jakubprzybytek/AstroWeather/sst/docs/api.md

# Main Forecast API

## Story

As an AstroWeather client, I want to request the forecast for a configured
location so that I can display its weather and astronomical events together for
the next six observing nights.

The endpoint presents one location-centric view. Clients should not need to
know which data is calculated on demand, which data is stored, or which weather
supplier produced it.

## Scope

For a valid `configurationId`, the main endpoint returns:

- the configuration identifier;
- the local date and time at which the response was rendered, which the
  device uses to synchronize its real-time clock;
- six observing nights, starting with the current night in the configuration's
  local timezone;
- local sunset and next-day sunrise times for each night;
- fixed-size hourly sun, moon, cloud, and precipitation matrices for each
  night, graded in four levels, with thunderstorms blinking;
- the supported display board identifier for each night;
- available maximum and minimum temperature for each night;

An observing night is the local-noon-to-local-noon window already used by
weather ingestion. Its `nightId` is the local calendar date on which the window
starts. For example, `nightId = 2026-09-17` covers local noon on September 17
through local noon on September 18.

## Endpoint

```http
GET /astro/{configurationId}
```

This is the main forecast endpoint, for signed-in web users. The device
calls the same handler as

```http
GET /device/astro/{configurationId}?key=<device key>
```

Both are served over HTTPS only. See
[Access control](architecture.md#access-control) for the credentials each
needs; without one the API answers `401` (no credential) or `403` (wrong
device key) instead of the payload.

### Demo configuration `test`

`GET /astro/test` (and `GET /device/astro/test` with the device key) returns a
made-up forecast that shows every display variant, for trying the boards out.
`test` is not in `configurations.ts` and is not listed by
`GET /configurations`; the web UI offers it on the Home view only, and the
device fetches it with `astro test` (or with `api path /device/astro/test`).
The payload is a normal protocol 3 response for six consecutive nights
(`forecast/demo.ts`):

- `time` is the real time in Europe/Warsaw, since the device sets its clock
  from it; `lastWeatherFetchTime` and the four aurora fetch times are `?`, and
  `refreshIntervalMinutes` is `360`.
- Sunset and sunrise start at random times and move by 1–3 minutes a night;
  the moon rises 40–60 minutes later each night. The sun and moon rows follow
  those times.
- Each night has a theme: clear sky with an aurora storm blinking "now";
  overcast with rain; thunderstorms clearing; a frosty evening clouding over
  with an aurora burst; every level and blink in turn; and missing data (gaps,
  whole-row `?`, unavailable temperatures and moon). Together the cloud,
  precipitation and aurora rows use every cell character.
- Temperatures cover one and two digits, both signs and zero (`4`, `-3`,
  `17`, `28`, `-14`, `0`), and `?`.

## Response Format

The endpoint is consumed by an STM32-based device without a JSON parser. A
successful request returns `text/plain; charset=utf-8` using the versioned ASCII
`key=value` protocol defined in [api-payload.md](api-payload.md).

The response contains the `protocol=3`, `configurationId`, `time`,
`lastWeatherFetchTime`, `lastGfzFetchTime`, `lastNoaaKpFetchTime`,
`lastNoaaOutlookFetchTime`, `lastOvationFetchTime` and `refreshIntervalMinutes`
header records, followed by six fixed-order display blocks. `time` is the configuration's local wall-clock time with its UTC
offset as `YYYY-MM-DDTHH:MM:SS.mmm+HH:MM`; `lastWeatherFetchTime` is the local
`YYYY-MM-DDTHH:MM:SS+HH:MM` of the last successful weather fetch, or `?`, and
the four aurora records are the same for each aurora feed. Each block contains, in order,
`display`, `board`, `nightId`, `numeric_0`, `numeric_1`, `matrix_0` through
`matrix_4`, `numeric_2`, and `numeric_3`. `numeric_0` and `numeric_1`
are sunset and sunrise; `matrix_0` through `matrix_4` are sun, moon, cloud,
precipitation and aurora; and `numeric_2` and `numeric_3` are maximum and minimum
temperature. `board` is `num4x4_matrix5x21` in version 3.
`refreshIntervalMinutes` is `60` on a storm night and `360` otherwise.

Records remain present when a source is missing or fails and use the payload
sentinel `?` for all unavailable times, weather values, and matrix slots. There is no
`displayCount` or end marker in version 3. The wire
format has one empty row between display blocks and no comments.

Error responses use the same line protocol and stable machine-readable error
identifiers. HTTP status codes remain authoritative.

## Behavior

### Forecast window

The handler determines the current `nightId` using the configuration's timezone
and the local-noon boundary. It returns that night plus the following five
nights in ascending `nightId` order.

The six-night window is stable around UTC midnight because it is derived from
the location's local time. Tests should inject the current time so the boundary
before and after local noon is deterministic.

### Response time

The `time` header record is the configuration's local wall-clock time, read
from the server clock after the forecast has been assembled so it is as close
as possible to the moment the response is sent. It uses the same IANA timezone
and DST rules as the forecast window, carries milliseconds, and ends in the UTC
offset in force at that instant (`+02:00`, `+01:00`), so a reader can tell
which zone it is in. The embedded device sets its real-time clock from the
wall-clock part.

### Last weather fetch time

`lastWeatherFetchTime` is the newest `fetchedAt` among the weather items used in
the response, converted to the configuration's local time, truncated to the
second, and followed by the UTC offset in force at the fetch. An ingestion run writes a night's item only after fetching and parsing
it, so a failed run leaves the value at the last success, and the value grows
old when ingestion keeps failing. It is `?` when no weather item is available.
The record is specific to weather: a future source adds its own record rather
than sharing this one.

### Last aurora fetch times

Each aurora feed has its own record, built the same way from the `fetchedAt`
of that feed's `#AURORA` items for the six nights served:

| Record | Feed | Item |
|---|---|---|
| `lastGfzFetchTime` | GFZ Hp60 forecast, nights 1–3 | `#AURORA#GFZ` |
| `lastNoaaKpFetchTime` | NOAA 3-day Kp forecast, nights 1–3 | `#AURORA#NOAA3` |
| `lastNoaaOutlookFetchTime` | NOAA 27-day outlook, nights 4–7 | `#AURORA#NOAA27` |
| `lastOvationFetchTime` | NOAA OVATION nowcast | `#AURORA#OVATION` |

The forecast job writes a feed's item only when that feed was fetched and
parsed, so one failing feed shows as an old time while the others stay
current; a single aurora record would hide that. The nowcast rewrites the
`OVATION` item each time it samples, which happens only on a storm night after
dark, so `lastOvationFetchTime` is normally `?`. A record is `?` when none of
the feed's items is there, and all four are `?` when the aurora read fails.
The `FLAG` item is not a feed and has no record. The demo configuration sends
`?` for all four.

### Astronomy

Astronomical events are calculated for each night from the configured latitude
and longitude. Sunset belongs to the date that starts the night, and sunrise
belongs to the following local date. Moonrise and moonset times are not
emitted; the moon is represented only by its hourly above-horizon matrix.

Sunset and sunrise are serialized as local `HH:MM` values. An event that does
not occur is represented by `?`. Sun and moon are graded for the 21
local-hour slots, 14:00 through 10:00 on the following date, by the minutes
of each hour the body is above the horizon: `0` for none, `1` for under half
an hour, `2` for half an hour or more, `3` for the whole hour. The altitude
is sampled at the middle of every minute. The 11:00-12:00 interval is not
displayed. The server emits the same 21 wall-clock slots across DST
transitions and maps each local hour to the appropriate instant.

`matrix_2` grades total cloud coverage: `0` only for a clear sky (0 %), and
the rest in thirds, `1` for 1-33 %, `2` for 34-66 % and `3` for 67-100 %.
`matrix_3` grades the precipitation probability in quarters (`0` for 0-24 % up
to `3` for 75-100 %), with `*` for a slot where a thunderstorm is predicted.
An available matrix contains exactly 21 characters, each `0`-`3`, `*` or `?`;
a matrix row with no available source data is represented by the single `?`
character.
Within an available row, `?` represents an unavailable individual slot. The
device shows `*` as its brightest level blinking; see
[api-payload.md](api-payload.md#matrix-encoding).

### Weather

Weather is read from the `ForecastData` DynamoDB table using the location
partition and requested night range:

```text
PK = LOC#<configurationId>
SK = NIGHT#<nightId>#WEATHER
```

Only `#WEATHER` records are part of the main API.

DynamoDB TTL removal is asynchronous. The reader must exclude an item when
`expireAt` is at or before the request time, even if DynamoDB has not deleted it
yet. Temperature extrema are calculated only from hourly values within the
requested observing night. The maximum is serialized in `numeric_2` and the
minimum in `numeric_3`, each rounded to whole degrees and written without a
decimal point (Clear Outside reports whole degrees).

### Graceful degradation

Astronomy and weather are assembled independently. Missing, expired, or failed
weather retrieval must not prevent available astronomy from being returned.
The affected weather matrix slots and weather-derived numeric values use `?`.

Likewise, an astronomy calculation failure must not prevent available weather
from being returned. The affected sunset and sunrise values and sun or moon
matrix slots use `?`.

The endpoint always returns all six display blocks with the complete fixed
record shape. It returns `500` only when it cannot assemble a trustworthy
protocol response at all; a failure isolated to astronomy or weather returns
`200` with sentinels only for the unavailable fields. Failures are logged with
their source and affected nights.

### Rate limiting and caching

API Gateway limits the API to a burst of one request and a steady-state rate of
one request per second. Requests beyond these limits are throttled by API
Gateway. The API does not currently emit cache headers or use response caching.

## Errors

| Status | Body | When |
|---|---|---|
| `200` | Forecast response | The configuration exists, including when astronomy or weather is partly unavailable |
| `404` | `error=configuration_not_found` response | The identifier is missing or unknown |
| `401` | `{"message":"Unauthorized"}` from API Gateway | No Cognito token on `/astro/...`, or no `key` on `/device/astro/...` |
| `403` | `{"message":"Forbidden"}` from API Gateway | Wrong device key |
| `429` | API Gateway's throttling response | Over the stage's one request per second |
| `500` | `error=forecast_unavailable` response | No trustworthy protocol response can be assembled |

The API does not expose upstream errors, AWS details, or stack traces to the
client. Operational details belong in structured Lambda logs.

## Acceptance Criteria

1. A request for a known configuration returns `200`, content type `text/plain`,
   protocol version 3, and exactly six display blocks in ascending order.
2. The first night is selected using the location's timezone and local-noon
   boundary; the next five night identifiers are consecutive local dates.
3. Every display block contains the complete, fixed-order record set defined in
   `api-payload.md`; each matrix is either `?` or exactly 21 valid characters.
4. Available, unexpired `#WEATHER` records supply the matching nights' minimum
   and maximum temperatures.
5. Expired, out-of-range, and other service records are not returned as weather.
6. Missing or failed weather does not remove a display block or available
   astronomy; its numeric values and unavailable matrix rows or slots use
   `?`.
7. An unknown configuration returns the versioned text error payload with
   status `404`.
8. Failed astronomy does not remove a display block or available weather; its
   times and unavailable sun or moon matrix rows or slots use `?`.
9. Unit tests cover the local-noon boundary, six-night range, item grouping,
   expired-item filtering, independent astronomy and weather failures, matrix
   encoding, sentinels, and serialization order.
10. An integration test verifies the deployed route for one known and one
   unknown configuration.
11. A successful response carries `time` as the configuration's local
   `YYYY-MM-DDTHH:MM:SS.mmm+HH:MM` at render time, with the offset of that
   instant, including after a DST change.
12. A successful response carries `lastWeatherFetchTime` as the local time and
   UTC offset of the newest weather `fetchedAt` used, or `?` without weather,
   and one such record per aurora feed, `?` for a feed without items.
13. Available `#AURORA` items supply `matrix_4`, merged as in
   [aurora-forecast-supplier.md](aurora-forecast-supplier.md#merging-sources);
   missing or failed aurora leaves it `?` and `refreshIntervalMinutes=360`
   without affecting the other rows.

## Data Attribution

The aurora row uses:

- the GFZ Hp60 and Kp forecasts, GFZ German Research Centre for Geosciences,
  licensed CC BY 4.0: Matzka, J., Bronkalla, O., Tornow, K., Elger, K. and
  Stolle, C. (2021), Geomagnetic Kp index, GFZ Data Services,
  doi:10.5880/Kp.0001; Matzka, J., Stolle, C., Yamazaki, Y., Bronkalla, O. and
  Morschhauser, A. (2021), The geomagnetic Kp index and derived indices of
  geomagnetic activity, Space Weather, doi:10.1029/2020SW002641;
- the 3-day Kp forecast, the 27-day outlook and the OVATION aurora nowcast of
  the NOAA Space Weather Prediction Center (public domain).

## Non-goals

- Backfilling or migrating old DynamoDB records.
- Fetching Clear Outside during an API request.
- Configuration CRUD or accepting arbitrary coordinates.
- Additional forecast services beyond weather and aurora.
- Guaranteeing that weather exists for every requested night.

## Clients

- **Embedded device**: calls `/device/astro/{configurationId}` with its key
  and parses the line protocol as described in
  [api-payload.md](api-payload.md).
- **Web UI**: a protocol inspection tool. It shows the HTTP status, content
  type, and response body verbatim, and deliberately does not parse the line
  protocol.
