jakubprzybytek/AstroWeather/firmware/HostControllerA/Docs/Console.md

# USB Console and Log

## Overview

The board enumerates as a USB CDC virtual COM port. That one port carries two
things:

- **The log.** Every task writes diagnostics through `LogService`, which is the
  only code that transmits on the port.
- **The console.** `ConsoleService` reads lines typed on the host, runs them as
  commands, and replies through the same log.

Both are HostController features. The DisplayController project has no USB and
no console yet; see [DisplayController](#displaycontroller).

The port, the client tools and recovering a port that has vanished are in
[Development.md](../../Docs/Development.md#connecting-over-usb-cdc).

## USB Device

The STM32G0B1's full-speed USB peripheral (`PA11`/`PA12`) runs ST's CDC class
from `USB_Device/`, generated by CubeMX. It enumerates as `VID_0483&PID_5740`
with a serial number built from the chip's unique ID (`Get_SerialNum()` in
`USB_Device/App/usbd_desc.c`), so Windows keeps giving it the same COM number.
`defaultTask` calls `MX_USB_Device_Init()` once the scheduler runs and then
exits; from then on USB runs from its interrupt.

| Item | Setting |
| --- | --- |
| Clock | HSI48, kept within USB's 0.25 % by the clock recovery system (CRS), synchronised to the host's start-of-frame packets. `main()` starts the CRS from `TRIM` 64; see [Development.md](../../Docs/Development.md#settings-that-must-survive-regeneration). |
| Interrupt | `USB_UCPD1_2_IRQn` at priority 1, above every other interrupt (all at 3); see [Architecture.md](Architecture.md#interrupt-priorities). |
| Receive | `CDC_Receive_FS()`, in the interrupt, hands each packet to `ConsoleService_OnUsbRxData()` and rearms reception. |
| Transmit | Only `LogService` calls `CDC_Transmit_FS()`; see [Log Service](#log-service). |
| Link power management | Off in the hardware configuration; no BOS descriptor, which suits a USB 2.00 device. |

**Why priority 1.** While an EP0 receive (`CTR_RX`) is still pending, the
peripheral does not answer a new SETUP packet, and the PC fails a request
after three quick tries. The display refresh interrupt holds the CPU for up to
about 170 us a thousand times a second, and a USB interrupt itself takes 100 to
290 us in the Debug build, so at the same priority Windows' requests were
sometimes missed: error 31 when opening the port, or a failed enumeration with
a new COM number. Above the refresh, USB is serviced at once.

The cost is on the display: a USB interrupt can now nest inside the refresh
interrupt, so the refresh's longest interrupt time in `status` can read several
hundred microseconds and a burst of USB requests can add a few late shifts.
Ordinary console use adds none. How the cause was found is in the
[archive](archive/USB_COM_Port_Investigation.md).

## Welcome Message

Opening the port prints a welcome, so a connected device is visibly alive even
with statistics off:

```text
[0:00:05:12] [INFO] OK connected to AstroWeather HostController, build 42, built 2026-09-23 10:12:40
[0:00:05:12] [INFO] Settings loaded from EEPROM: ok
[0:00:05:12] [INFO] 5 warnings/errors kept ('errors' lists them); newest: W 2026-09-27 12:19:50: DisplayBoard 0x14 unreachable status=1
[0:00:05:12] [INFO] Type 'help' for commands. Periodic stats are off; 'stats on' to switch.
```

The third line appears only while the [error log](#error-log) holds entries.

The build number and time come from `../Common/cmake/BuildInfo.cmake`, which
counts every build in `BUILD_NUMBER` and regenerates both, so they identify
the flashed image ([Development.md](../../Docs/Development.md#build)). The settings line gives
`Settings::Store::describe()` of the boot-time load (`ok`, `blank`,
`bad-crc`, ...; see [Settings.md](Settings.md#decode-results)). It is repeated
here because the startup log is written before USB has enumerated and never
reaches the host.

The welcome is triggered from two CDC class requests, hooked in the `USER CODE`
section of `USB_Device/App/usbd_cdc_if.c`:

| Request | Bridge call | Why |
| --- | --- | --- |
| `SET_CONTROL_LINE_STATE` | `ConsoleService_OnHostLineState(dtr)` | A rising edge of DTR. pyserial and `astro_console.py` raise DTR on open. |
| `SET_LINE_CODING` | `ConsoleService_OnHostLineCoding()` | Every terminal sets the line coding on open, including ones that never raise DTR, such as HTerm by default. |

Both only set a thread flag; the welcome is sent from the console task. A
program that sends both does so within milliseconds, so the task prints at most
one welcome per second (`kWelcomeHoldoffMs`). Changing the baud rate in a
terminal that is already open sends `SET_LINE_CODING` again and repeats the
welcome.

## Output Format

Every line on the port, a command reply or a log message, is a log record:

```text
[d:hh:mm:ss] [LEVEL] text
```

The prefix is uptime from `HAL_GetTick()`, with days unpadded. Command replies
are logged at `INFO`, so a reply looks like
`[0:00:05:20] [INFO] OK time-display=on`. The examples below leave the prefix
out.

| Level | Tag | ANSI colour |
| --- | --- | --- |
| `Info` | `INFO` | none |
| `Warn` | `WARN` | yellow, `ESC[33m` |
| `Error` | `ERR` | red, `ESC[31m` |
| `Debug` | `DEBUG` | dark grey, `ESC[90m` |

A coloured line is sent as `ESC[..m` + text + `ESC[0m` + `\n`.

Log messages from other tasks arrive interleaved with command replies. Replies
to a single command are queued together by the console task and are not split
by other output in practice, but asynchronous results, such as those of
`astro refresh`, follow later among ordinary log lines.

### ST67 driver messages

The ST67W6X network driver logs through `vLoggingPrintf()`, which
`User/Src/WiFi/St67HttpFetchTask.cpp` redirects into `LogService`. The driver's
`LOG_LEVEL` is `LOG_DEBUG` (`ST67W6X_Network_Driver/Target/logging_config.h`),
so its info and debug messages both appear, at the `DEBUG` level. Errors map to
`ERR` and warnings to `WARN`. The driver's file and line are dropped and each
message is truncated to 95 characters. Driver messages usually end in their own
`\n`, so they are followed by a blank line. Raw AT command logging
(`W61_AT_LOG_ENABLE`) is off.

## Log Service

`LogService` (`User/Src/Debug/LogService.cpp`) is a `Task<1536>` at normal
priority, started first in the HostController's `AstroWeather_Init()`.

Producers call `log()`, `logf()` or `sendLine()` from task context. The call
formats the prefix and message into a 256-byte record, puts it on a static
16-entry CMSIS queue without blocking, and wakes the task. If the queue is full,
the oldest record is discarded to make room; each lost record counts as
`dropped`. The calls are not ISR-safe.

The task drains the queue and hands each record to `CDC_Transmit_FS()`, the only
caller of that function in the application. While the transport reports
`USBD_BUSY` it retries every 5 ms, for up to 40 ms, then drops the record and
counts `busyDrop`. Any other failure also counts `busyDrop`. `CDC_Transmit_FS()`
reports busy before USB has enumerated, and the previous packet stays pending
while no program has the port open, so output written with the port closed is
lost rather than buffered. A queued record is removed before it is sent, so an
accepted record can still be lost here.

### Burst size

The console and log tasks have the same priority, so a command's whole reply is
normally queued before any of it is sent. A reply of more than 16 lines would
push its own first lines out. `help` and `errors` send through
`Console::PacedOutput` (`User/Src/Console/PacedOutput.cpp`), which pauses
30 ms after every 8 lines so the log task can drain the queue; `help all`,
over 200 lines, arrives whole. `status` is kept under 16 lines by a comment in
`StatusCommand.cpp`. `eeprom dump` prints 32 lines and relies on the log task
getting time between the I2C reads; a `dropped` count that rises during a dump
means lines were lost.

### Statistics

`stats on` switches on periodic telemetry: once immediately, then every 5
seconds on a fixed schedule, whatever else is being logged. It is off at every
boot and not saved. All of it is sent at the `Debug` colour and bypasses the
queue.

```text
[0:00:06:40] [STATS] sent=412 dropped=0 busyDrop=37
[0:00:06:40] [MEM] heapFree=24752 heapMin=19352
[0:00:06:40] [STACK] name=LogService configured=1536 remaining=652
[0:00:06:40] [STACK] name=ConsoleService configured=2816 remaining=1692
...
```

| Field | Meaning |
| --- | --- |
| `sent` | Queued records transmitted, command replies included. Statistics lines are not counted. |
| `dropped` | Records lost because the queue was full. |
| `busyDrop` | Lines lost because USB stayed busy or no host had the port open. Statistics lines are counted here. |
| `heapFree`, `heapMin` | `xPortGetFreeHeapSize()` and `xPortGetMinimumEverFreeHeapSize()`, in bytes. |
| `configured` | The task's stack size in bytes. |
| `remaining` | Stack high-water mark in bytes: the part of the stack never yet used. |

There is one `[STACK]` line for each task created through `Task<>`. The counters
are cumulative since boot. See [Firmware-RAM-Usage.md](Firmware-RAM-Usage.md)
for what the stack figures mean for sizing.

## Error Log

`LogService` keeps every message logged at `Warn` or `Error` in
`ErrorLog` (`User/Src/Debug/ErrorLog.cpp`), on top of printing it. That
includes the ST67 WiFi driver's own errors, which arrive through
`vLoggingPrintf()`. It is read with [`errors`](#errors) and summed up in the
[welcome message](#welcome-message), so a problem that happened while no
terminal was open, or before USB enumerated at boot, is still visible.

- **24 entries, ordered by latest occurrence.** The list runs from the entry
  quiet longest to the latest problem, which is also the "newest" the welcome
  message shows. When all 24 are used, the entry quiet longest is overwritten
  and counted as dropped, so a problem that keeps recurring is not pushed out
  by one-off ones.
- **Repeats are one entry.** A message identical to one already kept, at the
  same level, bumps that entry's count and last time and moves it to the end;
  its first time stays. So an error repeated every retry, or the five
  `DisplayBoard 0x1x unreachable` warnings of every refresh, take one entry
  each. Each entry stores a 16-bit hash of its text, so a new message is
  compared in full only against entries with the same hash.
- **Across resets.** An entry dated throughout and a dated repeat merge even
  across a reset, since a date means the same before and after it. Uptime
  restarts at every boot, so an entry with an uptime stamp, or a repeat
  logged before the clock is set, only merges within its own boot; each entry
  records the boot of its latest occurrence for that. The log therefore does
  not show that a merged problem spanned a reset.
- **Order without copying.** The 180-byte entries stay in their slots; a
  24-byte `order` list gives the slots by latest occurrence, so moving an
  entry to the end shifts at most 23 bytes with interrupts masked, not up to
  4.3 KB of entries.
- **Timestamps.** The local date and time when the clock is set, read from
  the RTC registers directly (`ClockTask::wallSecondsNow()`), without the RTC
  mutex, so a task that logs while holding it cannot deadlock. Until the clock
  is set, which after a power-up is the first astro refresh, entries carry
  uptime instead, marked `(previous boot)` or `(<n> boots ago)` when listed
  after a reset.
- **Text.** Up to 159 characters of the message; longer ones are cut. That
  keeps every warning and error whole except the longest ST67 statistics,
  such as `ST67 batch-final ...`.
- **Kept over a reset, a crash and reflashing, not a power loss.** The log
  lives in a 5 KB RAM region that the startup code neither initialises nor
  clears (`.noinit`, the last 5 KB of RAM, set up in `STM32G0B1xx_FLASH.ld`),
  at the same address in every build. At boot, `ErrorLog::Log::begin()` keeps
  it if its magic word and check word match and every entry is consistent,
  otherwise starts empty, and counts the boot. After a power loss the region
  is random and fails the check. A change to the entry layout must bump
  `ErrorLog::kVersion`, so an older layout is discarded rather than misread.
- **Cost.** Recording masks interrupts for the copy of one entry, under 200 bytes
  (the hash is computed before), so it is safe from any task or interrupt.
  Messages logged before `LogService::init()` are not recorded.

Only the HostController has the log.

## Console Service

`ConsoleService` (`User/Src/Console/ConsoleService.cpp`) is a `Task<2816>` at
normal priority.

### Receive path

1. `CDC_Receive_FS()` in `usbd_cdc_if.c` runs in the USB interrupt and passes
   each packet to `ConsoleService_OnUsbRxData()`, declared in
   `User/Inc/Console/ConsoleServiceBridge.h`, then rearms reception.
2. The bytes go into a 256-byte single-producer, single-consumer ring, and the
   task is woken. Bytes that arrive while the ring is full are discarded
   silently.
3. The task assembles lines from the ring:
   - `\r` is ignored and `\n` ends the line.
   - A line holds at most 127 characters. Anything longer is discarded up to
     the `\n` and answered with `ERR line-too-long`.
   - An empty line is ignored.
4. A complete line goes onto an 8-deep command queue. If it is full, the line is
   dropped with `ERR command-queue-full`.
5. The task runs queued commands one at a time, on its own stack.

Input is not echoed. The only output for a command is its reply.

### Dispatch

Each handler is tried in turn; the first that recognises the line owns it:

1. `help` (`HelpCommand.cpp`)
2. `errors [clear]` (`ErrorsCommand.cpp`), HostController only
3. `status` (`StatusCommand.cpp`)
4. `stats on`, `stats off` (in `ConsoleService.cpp`)
5. `astro ...` (`AstroCommand.cpp`), HostController only
6. `time ...` (`TimeCommand.cpp`), HostController only
7. `api ...` (`ApiCommand.cpp`), HostController only
8. `display low [on|off]` (`LowBrightnessCommand.cpp`), HostController only;
   ahead of `display`, which would take it as a bad argument
9. `adc ...` (`AdcCommand.cpp`)
10. `settings ...` and `wifi ...` (`SettingsCommand.cpp`)
11. `eeprom ...` (`EepromCommand.cpp`)
12. `display ...` (`DisplayCommand.cpp`)

A line no handler recognises gets `ERR invalid-command`. Commands are
case-sensitive. Fixed commands such as `stats on` or `settings show` must match
exactly, with single spaces; commands with numeric arguments are parsed with
`sscanf` and are more forgiving about spacing.

Handlers return a `Console::CommandResult`, and `ConsoleService` turns the
failures into these replies:

| Reply | Meaning |
| --- | --- |
| `ERR invalid-command` | No handler recognised the line. |
| `ERR invalid-argument` | The command was recognised but its arguments were not. |
| `ERR rtc-unavailable` | The RTC could not be read or written. |
| `ERR settings-unavailable` | No settings store, or the EEPROM write failed. A failed write is also logged as `[ERR] Settings save failed status=<n>`. |
| `ERR eeprom-unavailable` | No EEPROM in this variant, or the chip did not answer. |
| `ERR display-unavailable` | No display in this variant. |
| `ERR display-unreachable 0x1x`, `ERR unsupported-remote` | See [display](#display). |
| `ERR astro-refresh-busy`, `ERR astro-refresh-unavailable` | See [astro](#astro). |

Some handlers, `help`, `settings` and `wifi` among them, send their own more
specific `ERR` lines instead.

## Command Reference

Commands marked **HC** exist only in the HostController build. `help` lists
the same commands on the device.

### help

| Command | Reply |
| --- | --- |
| `help` | `OK help`, then every command's usage and one-line summary, by group. |
| `help <group>` | `OK help <group>`, then the group's commands, each with its summary, details and examples, then the group's notes. |
| `help <group> <command>` | `OK help <group> <command>`, then that command alone, e.g. `help display show` or `help time display`. The words must start the command's usage. |
| `help all` | `OK help all`, then every group in full, about 220 lines. |
| `help <unknown>` | `ERR unknown help group '<name>'; groups: status, stats, errors, display, astro, api, time, adc, settings, wifi, eeprom` |
| `help <group> <unknown>` | `ERR no help for '<group> <words>'; 'help <group>' lists its commands` |

The groups are `status`, `stats`, `errors` (HC), `display`, `astro` (HC),
`api` (HC), `time` (HC), `adc`, `settings`, `wifi` and `eeprom`.
`HelpCommand.cpp` holds the text as one table entry per command (usage,
summary, details) and per group (title, notes), so the index and the details
come from the same place. Replies are paced; see [Burst size](#burst-size).

### status

A one-screen summary, 15 lines on the HostController:

```text
OK status
firmware   HostController, build 42, built 2026-09-23 10:12:40
uptime     0d 00:03:11
heap       24752 B free, 19352 B lowest since boot
stats      off
eeprom     answering at 0x50, 512 bytes
settings   loaded at boot: ok; adc log off, adc display on, time display on, trim +0 ppm, low brightness off
wifi       'MyNetwork' stored; last connect ok 0d 00:03:05 ago (channel 2, -39 dBm)
astro      last refresh ok, 0d 00:02:25 ago, from console
weather    last fetched by the server 2026-09-23 09:05:12 +02:00, 1 h 07 min ago
aurora     last fetched by the server: GFZ 0 h 09 min ago, NOAA Kp 0 h 09 min ago, NOAA outlook 6 h 09 min ago, OVATION none
schedule   every 6 h from 00:10; next 12:10; last ok 2026-09-23 10:10
api        https://api.example.com/device/astro/wroclaw (built-in)
display    normal brightness; 3078 frames, 0 late shifts, 0 late interrupts, refresh interrupt up to 170 us
remote     0x10 host 0x11 no 0x12 no 0x13 no 0x14 no 0x15 no
```

| Line | Content and alternative forms |
| --- | --- |
| `firmware` | Variant, build number (`BUILD_NUMBER`) and build time. |
| `uptime` | `d hh:mm:ss` from the RTOS tick, which wraps after about 49 days. |
| `heap` | Free FreeRTOS heap now and the lowest it has been. |
| `stats` | `on, every 5 s` or `off`. |
| `eeprom` | Probed now: `answering at 0x50, 512 bytes` or `NOT ANSWERING at 0x50`. `not present in this variant` when there is no EEPROM; the `settings` and `wifi` lines are then left out. |
| `settings` | The boot-time decode result, then the values in use. |
| `wifi` | `not configured; set credentials with 'wifi set <ssid> <password>'`, or `'<ssid>' stored;` followed by `not connected since boot ('wifi test' to try)`, `last connect ok <age> ago (channel <n>, <rssi> dBm)` or `last connect FAILED <age> ago: <reason>`. The reasons are listed in [WiFi.md](WiFi.md). |
| `astro` **HC** | `no refresh since boot; try 'astro refresh'`, `first refresh running now`, or `last refresh <outcome>, <age> ago, from <trigger>`. Outcomes are `ok`, `fetch-failed`, `crc-failed`, `parse-failed` and `publish-failed`; a fetch failure adds its cause in brackets, such as `(no HTTP response)` or `(http 404)`. Triggers are `switch1`, `console`, `scheduled` and `wifi-test`. `; another running now` is appended while a refresh is in progress. |
| `weather` **HC** | When the server last fetched the weather, from the last good response, with its age if the clock is set. Otherwise `last fetch time unknown until a refresh succeeds`, `... not reported by the server`, `... malformed in the response`, or `none on the server at the last refresh`. |
| `aurora` **HC** | When the server last fetched each aurora feed, from the last good response: GFZ Hp60, NOAA 3-day Kp, NOAA 27-day outlook and the OVATION nowcast. Each shows its age if the clock is set, else `MM-DD HH:MM`; `none` when the server had no data from that feed (OVATION is normally `none`: it is fetched only on storm nights), `not sent` from a server without the record, or `malformed`. `last fetch times unknown until a refresh succeeds` before that. See [api-payload.md](../../../sst/docs/api-payload.md). |
| `schedule` **HC** | The next slot and the last success. `next` reads `once the clock is set` before the time is known; after failures it reads `retry <n> in <s> s`, `retry <n> now` or `no WiFi credentials, then <HH:MM>`. `last ok` reads `none since power-up` until a refresh succeeds. See [AstroRefresh.md](AstroRefresh.md). |
| `api` **HC** | The URL the next fetch uses, `(saved)` if `api host` or `api path` is saved, else `(built-in)`. See [api](#api). |
| `display` | `normal brightness` or `low brightness`, the state in use; it normally matches `low brightness` in the `settings` line, since both controls save (see [display low](#display)). Then the local board's refresh, since boot: frames shown (50 a second), refresh interrupts that came later than a whole pass (`late shifts`) or than the pass they start (`late interrupts`), and the longest refresh interrupt. See [Display.md](../../Docs/Display.md#refresh-operation). |
| `remote` | The chain addresses `0x10`–`0x15`, one per forecast block ([AstroRefresh.md](AstroRefresh.md#display-mapping)): `host` at the host's own strap address, otherwise the remote board there, probed now on I2C, `yes` if it answered. A host strapped outside the chain gets `; host 0x16 has no block` (its address) at the end. `no display boards in this variant` without a display. |

WiFi has no link state of its own, so the `astro` line is the evidence that the
network path works.

### stats

| Command | Reply |
| --- | --- |
| `stats on` | `OK stats=on`, then an immediate report and one every 5 s. |
| `stats off` | `OK stats=off` |

See [Statistics](#statistics) for the report format.

### errors

**HC.** The [error log](#error-log): the last warnings and errors, kept over
resets.

| Command | Reply |
| --- | --- |
| `errors` | `OK errors <n> of 24 kept, <d> older dropped, boot <b>`, then one line per entry, ordered by latest occurrence: the one quiet longest first, the latest problem last. |
| `errors clear` | `OK errors cleared`. Empties the log and the dropped count; the boot count stays. |
| `errors <anything else>` | `ERR invalid-argument` |

```text
OK errors 3 of 24 kept, 0 older dropped, boot 6
E up 0d 00:00:42 (previous boot): CurrentSense ADC conversion failed
W 2026-09-27 12:19:50: DisplayBoard 0x10 unreachable status=1
E 2026-09-27 13:30:02 4x, first 2026-09-27 12:20:31: AstroDataRefresh fetch status=...
```

Each line is the level (`E` error, `W` warning), when it was last logged, and
for a repeat `<count>x, first <time>`, then the message as it was logged,
without the log line's own `[uptime] [LEVEL]` prefix. An uptime stamp from an
earlier boot is marked `(previous boot)` or `(<n> boots ago)`. A repeat moves its entry
to the end, so the list reads in order of each entry's latest occurrence: the
last line is always the latest problem, and in the example the `fetch` error
last happened after the other two although it first happened between them. The list is sent
through `PacedOutput` ([Burst size](#burst-size)), so all 25 lines fit through
the 16-line log queue.

### astro

**HC.** Details in [AstroRefresh.md](AstroRefresh.md).

| Command | Reply |
| --- | --- |
| `astro refresh` | `OK astro-refresh=started`. The fetch runs in the background; progress and the result follow in the log. |
| `astro test` | `OK astro-refresh=started`. As `astro refresh`, but fetches the server's demo forecast (`/device/astro/test`, with the key) once, which shows every display variant; the saved path, the schedule and the weather status are unchanged. |

`ERR astro-refresh-busy` means a refresh is already running, and
`ERR astro-refresh-unavailable` that the refresh task is not ready. Any other
line starting with `astro` gets `ERR invalid-argument`. The refresh task logs
`AstroDataRefresh trigger accepted source=console` (or
`... ignored: active source=console` as a warning) just before the reply.

### api

**HC.** The server the astro refresh fetches from. Details in
[WiFi.md](WiFi.md#server).

| Command | Reply |
| --- | --- |
| `api` or `api show` | Three lines: `OK api host=<host> (saved\|built-in)`, `OK api path=<path> (saved\|built-in)` and `OK api key=<set>\|<none> (saved\|built-in)`. The key itself is never shown. |
| `api host <host>` | `OK api-host=<host>`. A bare host name, 1–64 characters, no scheme, port, path or whitespace. Saved. |
| `api path <path>` | `OK api-path=<path>`. Starts with `/`, 1–32 characters, no whitespace. Saved. |
| `api key <key>` | `OK api-key=<set>`. The API's device key, 1–32 letters, digits or `- _ . ~`. Saved; sent as `?key=<key>` after the path. |
| `api default` | `OK api-default`, then the `api show` lines. Forgets the saved host, path and key. |

Each part not saved uses its built-in value, `APP_ST67_HTTP_HOST`,
`APP_ST67_HTTP_PATH` or `APP_ST67_HTTP_KEY` from `app_credentials.h`; with no
key at all the request carries none. The API (see
`sst/docs/architecture.md#access-control`) wants path
`/device/astro/<configurationId>` and the stage's `DeviceApiKey`. A change
applies from the next fetch and does not start one; run `astro refresh` to try
it. A wrong path shows up there as `fetch-failed (http 404)`, a missing key as
`http 401` and a wrong one as `http 403`. The fetch log line shows the key only
as `key=<set>` or `key=<none>`.

A value that breaks the rules is refused with the reason, for example
`ERR api-host: give the bare host name, without http:// (HTTP only, port 80), ...`
`ERR api-path: must start with / and be 1-32 characters with no spaces, ...`
or `ERR api-key: must be 1-32 letters, digits or - _ . ~`.
`api host`, `api path` or `api key` with no value gets `ERR api-host: missing value. ...`,
any other `api` line `ERR unknown command '<line>'; see 'help api'.`, and a
failed save `ERR settings-unavailable`.

### time

**HC.** The clock commands are detailed in [RTC.md](RTC.md#console-commands),
`time hsi` and `time sync` in
[TimelineSync.md](../../Docs/TimelineSync.md#the-hosts-clock).

| Command | Reply |
| --- | --- |
| `time show` | `OK time=2026-10-09 22:26:10.284 set=yes trim=+0ppm prediv=124/5999 calm=0` |
| `time set <YYYY-MM-DD> <HH:MM[:SS]>` | `OK time=2026-09-23 10:15:00`. Seconds default to `00`. |
| `time trim <ppm>` | `OK time-trim=+12ppm`. The RTC crystal's error, range ±1000. Saved. |
| `time display on\|off` | `OK time-display=on` or `OK time-display=off`. Saved. |
| `time hsi` | `OK time-hsi=63 cal=0x8E saved=63`: the host's HSI16 trim (`HSITRIM`) in use, `HSICAL` as read back, and the saved trim. |
| `time hsi <0-127>` | Sets the HSI16 trim; the same reply. Applies at once and at boot. Saved. No effect: the host runs from its crystal and HSI16 clocks nothing. |
| `time sync` | `OK time-sync sent=2 answered=0 last=9s-ago next=15s burst`: the timeline sync broadcasts sent, those at least one display board acknowledged, the age of the last, the time to the next, and `burst` or `every-120s`. Each board that answered the last status poll is appended as ` 0x11=locked` or ` 0x11=wants-sync`, with `+needs-content` added while the board asks for its content, which the host then re-sends ([Display.md](Display.md#the-display-aggregate)). |
| `time sync now` | `OK time-sync=burst`: starts a burst of syncs, unless one is running. |

`set=no` in `time show` means the clock has not been set since a power loss.
The `prediv` and `calm` values depend on the trim; see
[RTC.md](RTC.md#trimming). The host's clock and how to measure it are in
[TimelineSync.md](../../Docs/TimelineSync.md#the-hosts-clock). An invalid date or
time, a trim out of range, an HSI trim above 127, or any other `time` line gets
`ERR invalid-argument`.

### adc

Details in [CurrentSense.md](CurrentSense.md).

| Command | Reply |
| --- | --- |
| `adc log on\|off` | `OK adc-log=on` or `OK adc-log=off`. Logs a current-sense reading ten times a second. |
| `adc display on\|off` | `OK adc-display=on` or `OK adc-display=off`. Shows the current on numeric display 2. |

Both are saved to the EEPROM at once. Any other `adc` line gets
`ERR invalid-command`.

### settings

Details in [Settings.md](Settings.md).

| Command | Reply |
| --- | --- |
| `settings show` | Six lines, shown below. |
| `settings save` | `OK settings-save` |
| `settings defaults` | `OK settings-defaults` |

```text
OK settings adc-log=off adc-display=on time-display=on time-trim=+18400ppm time-hsi=64 display-low=off
OK settings wifi-ssid=MyNetwork wifi-password=<set>
OK settings api-host=<built-in>
OK settings api-path=/device/astro/wroclaw
OK settings api-key=<set>
OK settings boot-load=ok
```

`settings show` prints the values the firmware is using. The password appears
only as `<set>` or `<unset>`, and an empty SSID as `<unset>`. An API host or
path that is not saved shows as `<built-in>`; the key shows as `<set>` or
`<built-in>`, never its value. `boot-load` is
what the EEPROM held at power-up, not its present content.

`settings save` rewrites the stored copy, which is needed only after
`boot-load` reported an error or after `eeprom erase`; the other commands save
as they change. `settings defaults` resets every value and saves: adc log off,
adc display on, time display on, trim 0, HSI trim 64, normal brightness, no
WiFi, built-in API host and path. The running tasks keep their current behaviour until the
next boot, except the API target, which the next fetch reads.

Any other line starting with `settings` gets
`ERR unknown command '<line>'; see 'help settings'.`

### wifi

Details in [WiFi.md](WiFi.md).

| Command | Reply |
| --- | --- |
| `wifi set <ssid> [password]` | `OK wifi-set ssid='<ssid>' password=<set>; saved.`, or `... no password (open network); saved.` Then, on the HostController, a connection test starts. |
| `wifi test` | `OK wifi-test`, then a connection test. |
| `wifi clear` | `OK settings-wifi-clear` |
| `wifi stress` | `OK wifi-stress mode=<m> cycles=<n>` and an explanation, then the bench batch from [WiFi.md](WiFi.md#stress-batch): `<n>` connect, DHCP, fetch, disconnect cycles about 1 s apart (about 25 min for 100), each logging `ST67 cycle=...`, then `ST67 batch-final ...` and the module powered down. Refreshes are refused as `Busy` meanwhile; it cannot be stopped. A second `wifi stress` while one runs is ignored with `ST67 batch trigger rejected: active` at the end. |

`wifi set` rules:

- The SSID is 1–32 characters. The password is 8–63 characters, or left out
  for an open network.
- An argument is a run of non-space characters, or a double-quoted string that
  may contain spaces: `wifi set "My Network" "my pass phrase"`. There is no
  escape for a `"` inside a value.
- Invalid input is rejected with a specific `ERR wifi-set: ...` line before
  anything is saved: a missing SSID, an unterminated quote, a value too long or
  too short, or more than two arguments.
- The whole line must fit the 127-character limit, which a quoted 32-character
  SSID and a quoted 63-character password do.

The test runs an ordinary astro refresh tagged `wifi-test`, so it also
publishes the forecast to the displays. It first replies
`Testing the connection to '<ssid>' now; the result follows in a few seconds.`,
or explains that a refresh is already running or the WiFi task is not ready.
The verdict follows as a log line such as
`WiFi test passed: connected to '<ssid>' (channel 2, -39 dBm) and fetched the forecast.`
or `WiFi test FAILED for '<ssid>': wrong password.`

`wifi test` with nothing stored replies
`ERR wifi-test: no credentials stored. Set them with 'wifi set <ssid> <password>'.`
Any other line starting with `wifi` gets
`ERR unknown command '<line>'; see 'help wifi'.`

### eeprom

Raw access to the 512-byte 24AA04 settings EEPROM at `0x50`, for bring-up and
debugging. Offsets and lengths are hex, matching the addresses `eeprom dump`
prints. `000`–`0FF` holds the settings image; see
[Settings.md](Settings.md#image-layout).

| Command | Reply |
| --- | --- |
| `eeprom probe` | `OK eeprom-probe addr=0x50 size=512 page=16` |
| `eeprom scan` | `OK eeprom-scan found=0x50` for each device on I2C1, then `OK eeprom-scan devices=<n>`. The board's own slave address, `0x08`, is skipped. |
| `eeprom dump` | 32 lines of 16 bytes, `000: FF FF ...` to `1F0: ...`, with no `OK` line. |
| `eeprom read <offset> [length]` | The same hex lines for that range. `length` defaults to 1. |
| `eeprom write <offset> <hex>` | `OK eeprom-write offset=0x100 bytes=3`. Up to 32 bytes as an even number of hex digits without spaces, e.g. `eeprom write 100 A55A01`. |
| `eeprom erase` | `OK eeprom-erase`. Fills all 512 bytes with `FF`. |

A range past the end of the chip, malformed hex, or an unknown `eeprom` line
gets `ERR invalid-argument`. A chip that does not answer gets
`ERR eeprom-unavailable`. `eeprom erase` wipes the settings: the next boot uses
defaults unless `settings save` is run first. `eeprom write` into `000`–`0FF`
changes the stored settings, and a bad CRC makes the next boot fall back to
defaults.

The scan finds the EEPROM on all of `0x50`–`0x57` and every remote
display board that is present; see [Settings.md](Settings.md#storage-medium).

### display

`show`, `row`, `blink`, `level`, `test` and `clear` take an optional board
between `display` and the subcommand:

- none: the local board, through `Display::submitLocal()`;
- `0x10`–`0x15`: the board at that address, as `status` and the
  `DisplayBoard 0x1x unreachable` warnings name it, through
  `Display::submitRemote()`. The host's own address is the local board; any
  other address is `ERR invalid-argument`;
- `all`: every board, the local one included.

For example `display 0x12 test`, `display 0x14 show 1 12.3`,
`display all clear`. The command changes the host's buffered copy of a remote
board and sends that board its whole state, so the rest of its forecast stays.
The next `astro refresh` (or scheduled one) redraws every board and replaces
it. `passes` is the local board's only: the I2C messages carry no pass table,
so with a remote target or `all` it replies `ERR unsupported-remote`.
`display low` drives every board already and takes no target. The content,
blink and level model is in [Display.md](../../Docs/Display.md#public-interface).

| Command | Effect |
| --- | --- |
| `display show <n> <value>` | Numeric display `n` (0–3) shows `value`: a number with up to three decimals (`12.34`, `-45`, `0.5`; the decimals set the precision, −999.9 to 9999), a time `HH:MM` (00–99 each, not checked as a clock), `?` for the unavailable pattern (the decimal point on all four digits) or `blank`. |
| `display row <r> <cells>` | Matrix row `r` (0–4, 0 at the top), one character per column as the forecast payload sends them: `0`–`3` the level, `a`–`c` levels 1–3 blinking, `*` full and blinking, `.` or `?` off. Missing columns are off; more than 21 is an error. `display row 0 0123abc*0123abc*012300` shows every kind. |
| `display blink <n> off\|colon\|all` | Nothing, the colon (L1 and L2), or every segment of display `n` blinks. |
| `display level <n> <0-3>` | Brightness level of display `n`, all segments; 3 is full. |
| `display test` | Every element lit: the levels run 0 to 3 along the matrix columns and along the sixteen digits, and every level also blinks next to the same level steady. On the numerics, each digit's decimal point blinks at the digit's level and the colons blink at level 3. On the matrix, rows 0, 2 and 4 are steady, row 1 blinks throughout, and row 3 blinks in the odd columns (1, 3, 5, ...), counting from 1. To judge the levels and blinking by eye. |
| `display clear` | Everything on the board off, nothing blinking, every level full. |
| `display passes [<a> <b> <c> <d>]` | Shows the pass lengths behind the levels, as `OK display passes=12/31/27/30`, or sets them: percent of a slot, summing to 100. Takes effect at once; not saved. For tuning by eye; see [Display.md](../../Docs/Display.md#blink-and-brightness-levels). |
| `display low on\|off` **HC** | Low brightness on every board: drives `LOW_POWER_ENABLE`. Saved, and applied at boot. Replies `OK display-low=on` or `OK display-low=off`. |
| `display low` **HC** | `OK display-low=<in use> saved=<saved>`, e.g. `OK display-low=on saved=on`. Switch 2 also saves, so the two differ only if a save failed, which logs `Settings save failed`. |

The other commands reply `OK display` with no target, `OK display 0x12` with
one, and `OK display all` for every board. A remote board that does not take
the update after the usual three attempts gets `ERR display-unreachable 0x12`,
or, with `all`, a list after the reply: `OK display all; unreachable 0x13 0x14`.
Its buffer keeps the change either way. Out-of-range values, a bad cell, a bad
target or an unknown `display` subcommand get `ERR invalid-argument`; with
`all`, a bad argument changes no board. On the local board, display 2 is also
driven by the current readout and display 3 by the clock, and the bottom
matrix row by refresh progress, so a manual setting there may soon be
overwritten. Nothing but a refresh writes a remote board.

## Security

The WiFi password is stored in the EEPROM in the clear.

- `wifi set` is **not** echoed. The console does not echo input, and the reply
  and connection test log only the SSID. The driver's AT command log, which
  would contain the password, is compiled out.
- `settings show` and `status` never print the password. `api show`,
  `settings show` and the fetch log never print the API key either; the key
  is in the EEPROM in the clear as well, and the typed `api key` line passes
  through the host's terminal like `wifi set`.
- `eeprom dump` and `eeprom read` over the settings area print it as hex bytes.
- The typed line does pass through the host's terminal, its scroll-back and any
  capture file.

Anyone with the USB port can also read and change the credentials, since the
console has no authentication.

## DisplayController

The DisplayController is a separate project (`../DisplayController`) on an
STM32G070, which has no USB, and it does not build the console or the log. A
console over USART2 is planned; see
[Display_Board_Purchasing.md](../../../KiCad/Docs/Display_Board_Purchasing.md#console-over-uart).
`ConsoleService` keeps its `ERR display-unavailable`, `ERR eeprom-unavailable`
and `ERR settings-unavailable` replies for a start without those devices.

## Fixed Limits

| Resource | Limit | Where |
| --- | ---: | --- |
| Console task stack | 2816 bytes | `ConsoleService.hpp` |
| RX ring | 256 bytes | `kRxRingSize` |
| Command line | 127 characters | `kMaxLineLength` = 128 |
| Command queue | 8 lines | `kCommandQueueDepth` |
| Welcome hold-off | 1 s | `kWelcomeHoldoffMs` |
| Console reply | 127 characters | `ConsoleService::reply()` buffer |
| Log task stack | 1536 bytes | `LogService.hpp` |
| Log queue | 16 records | `kLogQueueDepth` |
| Log record | 255 characters, prefix included | `kMaxLogMessageLen` = 256 |
| Error log | 24 entries of up to 159 characters | `ErrorLog::kCapacity`, `kTextSize` = 160 |
| ST67 driver message | 95 characters | `vLoggingPrintf()` buffer |
| CDC busy retry | every 5 ms, for up to 40 ms | `kTxRetryDelayMs`, `kTxRetryWindowMs` |
| Statistics period | 5 s, while `stats on` | `kStatsPeriodMs` |

Longer text is truncated by `snprintf`.

## Code Layout

| File | Content |
| --- | --- |
| `User/Src/Debug/LogService.cpp` | Log queue, CDC transmit, statistics. |
| `User/Src/Console/ConsoleService.cpp` | RX ring, line assembly, command queue, dispatch, welcome. |
| `User/Inc/Console/ConsoleServiceBridge.h` | C entry points called from `usbd_cdc_if.c`. |
| `User/Src/Console/*Command.cpp` | One handler per command group; `LowBrightnessCommand.cpp` takes `display low` ahead of `DisplayCommand.cpp`. |
| `User/Src/Debug/FirmwareInfo.cpp` | Firmware name and build time for the welcome and `status`. |
| `USB_Device/App/usbd_cdc_if.c` | CubeMX CDC glue; changes only inside `USER CODE` sections. |
| `tools/astro_console.py` | Host client. |

## Maintenance Notes

- Keep `CDC_Transmit_FS()` in `LogService` alone. New output goes through the
  log queue, not straight to the transport from another task or an interrupt.
- Keep the C bridge. CubeMX-generated C code must not include C++ headers.
- The log API is for task context. Logging from an interrupt would need an
  ISR-safe producer; only the USB RX path runs in interrupt context today.
- A new command's reply must stay under 16 lines, or be split as `help` is.
- Add a new command group to the dispatch chain in `ConsoleService::execute()`,
  to the `help` index and groups, and to this document.
- Changing a queue, ring or line limit changes static RAM use; update the
  [Fixed Limits](#fixed-limits) table and
  [Firmware-RAM-Usage.md](Firmware-RAM-Usage.md).
