jakubprzybytek/AstroWeather/firmware/HostControllerA/Docs/Settings.md

# Persistent Settings

## Overview

The Host Controller keeps a small set of user-configurable settings in an
on-board EEPROM so that they survive a power cycle. Settings are read once
during startup and applied to the owning tasks before the scheduler runs, and
they are written back immediately whenever a console command or switch 2
changes one.

Currently persisted:

- Current-sense logging on/off (`adc log`).
- Current-sense display output on/off (`adc display`).
- Clock display on/off (`time display`).
- Clock trim, the measured error of the RTC's crystal clock in ppm (`time trim`).
- HSI trim, the HSI16 `HSITRIM` value 0-127 (`time hsi`); no effect since the
  host runs from its crystal.
- Low brightness (`display low`, switch 2).
- WiFi SSID and password.
- API host and path (`api host`, `api path`).

The storage format is designed so that adding a further setting requires no
format version change and no migration code. That property is the main subject
of this document, and the rules that preserve it are listed under
[Adding a new setting](#adding-a-new-setting).

## Storage Medium

| Property | Value |
| --- | --- |
| Part | Microchip 24AA04HT-I/OT, datasheet DS20002119 |
| Bus | I2C1, shared with the remote display boards; see [I2C.md](../../Docs/I2C.md) |
| Device address | `0x50`, 7-bit |
| Capacity | 512 bytes, as two 256-byte blocks |
| Page size | 16 bytes |
| Write cycle | 5 ms maximum |
| Write protect | WP tied to ground: whole array writable |

The control byte is `1010 x x B0`. The `x` bits are don't-care because the
SOT-23-5 package has no address pins, and `B0` selects the block, so the part
acknowledges the whole range `0x50`–`0x57`: even addresses reach block 0
(`000h`–`0FFh`) and odd addresses block 1 (`100h`–`1FFh`). Treat all eight
addresses as reserved when assigning addresses to other devices on the bus.

Sequential reads run through the entire array, across the block boundary, in a
single transaction. Page writes do not: a write crossing a 16-byte page wraps to
the start of that page. Since 256 is a multiple of 16, a page never straddles a
block.

The `H` variant's WP pin protects the upper block (`100h`–`1FFh`) when tied
high. On this board it is tied to ground.

The part was verified on hardware, not only from its marking: distinct values
written at `0F8h`, `178h` and `1F8h` read back independently, with `078h`
unchanged, which a 128-byte 24AA01 cannot do; a single 16-byte transaction
landed without wrapping; and one read spanning `0F8h`–`107h` returned the bytes
written through block 1.

Access goes through `Device::Eeprom24AA04`, which splits writes on page
boundaries, places bit 8 of the offset in `B0`, and polls for the internal write
cycle. That driver in turn uses `Device::I2cBus`, which holds the mutex
serializing all I2C1 traffic ([I2C.md](../../Docs/I2C.md#host-side)).

## Image Layout

The settings image is a fixed 256-byte region at offset `000h`, the lower
block of the part. The upper 256 bytes are unused. A fixed header carries
integrity information, and the payload after it is a sequence of
variable-length records.

An image written by older firmware with a 128-byte region is also a valid
256-byte image, with no version bump or migration: the CRC covers only the
version, `payloadLen` and the `payloadLen` bytes of payload, never the padding
behind them. Whatever the bytes behind
it held, such as test data from raw `eeprom write`s, is ignored. 256 is the
limit for this header, because `payloadLen` is a single byte. See
[When the version must change](#when-the-version-must-change).

```
offset  size  field
0x00    2     magic       'A' 'W'
0x02    2     crc16       big endian, see below
0x04    1     version     container format version, currently 1
0x05    1     payloadLen  number of payload bytes that follow
0x06    N     payload     sequence of tag/length/value records
0x06+N  ...   padding     0xFF to the end of the 256-byte image
```

The CRC deliberately sits *before* the fields it protects so that everything it
covers is a single contiguous range, which keeps the implementation to one call.

### CRC

CRC-16/CCITT-FALSE:

| Parameter | Value |
| --- | --- |
| Polynomial | `0x1021` |
| Initial value | `0xFFFF` |
| Input reflected | no |
| Output reflected | no |
| Final XOR | none |

It covers `version`, `payloadLen` and the payload, that is bytes `0x04` through
`0x05 + payloadLen`. It does **not** cover the magic or the padding.

Implemented in software rather than using the STM32 CRC peripheral, so that the
feature needs no `.ioc` change. See [Development.md](../../Docs/Development.md)
for the CubeMX rules.

### Payload records

Each record is:

```
tag     1 byte
length  1 byte    number of value bytes, 0x00..0xFE
value   `length` bytes
```

Records run consecutively with no alignment or padding. A tag of `0xFF`
terminates the sequence. That value is chosen because an erased EEPROM byte
reads `0xFF`, so a blank or over-short payload terminates naturally rather than
needing an explicit end marker to be written.

## Tag Registry

This table is the authoritative allocation. `User/Inc/Settings/SettingsCodec.hpp`
must match it.

| Tag | Name | Length | Value |
| --- | --- | --- | --- |
| `0x01` | `AdcFlags` | 1 | Bit 0 = current-sense logging enabled, bit 1 = current-sense display enabled. Remaining bits reserved, write 0. |
| `0x02` | `ClockTrim` | 4 or 5 | Bytes 0-3: signed RTC clock error in ppm, big endian; see [RTC.md](RTC.md#trimming). Byte 4, optional: the HSI trim, `HSITRIM` 0-127; see [TimelineSync.md](../../Docs/TimelineSync.md#the-hosts-clock). Written when either is not its default (LSI trim 0, HSI trim 64); the fifth byte only when the HSI trim is not 64. A fifth byte above 127 is ignored (HSI trim 64). An older build reads the first four bytes and ignores the fifth. |
| `0x10` | `WifiSsid` | 1–32 | SSID bytes, not NUL terminated. |
| `0x11` | `WifiPassword` | 1–63 | Passphrase bytes, not NUL terminated. |
| `0x12` | `ApiHost` | 1–64 | API server host name, not NUL terminated. Absent: the built-in `APP_ST67_HTTP_HOST`. |
| `0x13` | `ApiPath` | 1–32 | API path starting with `/`, not NUL terminated. Absent: the built-in `APP_ST67_HTTP_PATH`. A longer record, which older firmware allowed up to 64, is ignored on decode (built-in path) rather than cut short. |
| `0x14` | `ApiKey` | 1–32 | API device key, letters, digits and `- _ . ~`, not NUL terminated; sent as `?key=`. Absent: the built-in `APP_ST67_HTTP_KEY`. |
| `0x20` | `ClockFlags` | 1 | Bit 0 = clock shown on local numeric display 3. Remaining bits reserved, write 0. Written only when it differs from the default, so normally absent. |
| `0x21` | `DisplayFlags` | 1 | Bit 0 = low brightness (`LOW_POWER_ENABLE` driven high); see [Display.md](Display.md#low-brightness). Remaining bits reserved, write 0. Written only when set. |
| `0xFF` | *reserved* | — | End of records. Never allocate. |

Suggested grouping for future allocations, to keep related settings together:

| Range | Use |
| --- | --- |
| `0x01`–`0x0F` | Local device behaviour |
| `0x10`–`0x1F` | Network and credentials |
| `0x20`–`0x2F` | Display behaviour |
| `0x30`–`0xFE` | Unallocated |

## Adding a new setting

The format is built so this is routine. Adding a setting does **not** change
`version` and does **not** need migration code, because content written before
the setting existed simply has no record for the new tag, and the decoder leaves
that field at its compile-time default.

1. Allocate the next free tag in the appropriate range and add a row to the
   [Tag Registry](#tag-registry) above. Never reuse a retired tag.
2. Add the enumerator to `Settings::Tag` in
   `User/Inc/Settings/SettingsCodec.hpp`.
3. Add the field to `Settings::Values`, **with a default that matches the
   behaviour the firmware has when nothing is stored**. See
   [Defaults](#defaults).
4. In `encode()`, append the record. If the setting is at its default or
   otherwise unset, prefer to write no record at all; that is what keeps unused
   settings free. See [Space budget](#space-budget).
5. In `applyRecord()`, handle the new tag. Validate `length` before reading the
   value; a record on the chip may be any length.
6. Apply the value at startup in `AstroWeather_Init()`, before the owning task is
   started.
7. Persist it from whichever console command changes it, by updating
   `store.values()` and calling `store.save()`. If a task other than the
   console reads or writes the field, add a setter or copier on `Store` that
   takes `mutex_`, as `setLowBrightness()` and `copyApiTarget()` do.
8. Add native test cases to `tests/SettingsCodecTests.cpp`. At minimum a round
   trip, and a case proving an image written *without* the new record still
   decodes and leaves the new field at its default.
9. Check the worst-case size still fits. See [Space budget](#space-budget).

### When the version must change

Bump `kContainerVersion` only if the **container** changes, not when settings
are added or removed. That means a change to the header layout, the CRC
algorithm or coverage, the image location, or the record framing itself, or a
payload over 255 bytes, which needs a wider `payloadLen`. Growing the image up
to 256 bytes is not one of them (see [Image Layout](#image-layout)). Such a
change should be rare. A decoder that meets a version it does not recognise reports
`BadVersion` and falls back to defaults, so an unexpected bump silently discards
the user's settings.

### Invariants

These must hold for the compatibility rules above to work.

- **Tag numbers are permanent.** Once assigned, a tag never changes meaning.
  Retire a setting by abandoning its tag, never by recycling it.
- **Unknown tags are skipped, not rejected.** This lets an older build read a
  chip written by a newer one.
- **An absent record means "use the default"**, never "invalid".
- **Decoding always leaves `Values` fully populated**, on every exit path,
  including failures.

## Decode Results

`Settings::decode()` reports one of the following. In every case other than
`Ok`, `Values` holds the compile-time defaults.

| Result | Meaning | Typical cause |
| --- | --- | --- |
| `Ok` | Image parsed | — |
| `Blank` | First two bytes are `0xFF` | Never-written chip |
| `BadMagic` | Magic is neither `AW` nor erased | Foreign data, wrong offset |
| `BadVersion` | Container version not understood | Written by newer firmware |
| `BadLength` | `payloadLen` exceeds the array | Corruption |
| `BadCrc` | CRC mismatch | Corruption, torn write |
| `Truncated` | A record runs past `payloadLen` | Corruption |

`Settings::Store::load()` collapses these into `Ok`, `Defaulted` or
`ReadFailed`, and keeps the detailed result available through `lastDecode()`
for logging. `settings show` reports it as `boot-load=`, `status` in its
`settings` line, and the console's welcome message as
`Settings loaded from EEPROM: <result>`. All three describe what was found at
startup, not the chip's present content.

An EEPROM **read failure** at startup also sets `lastDecode()` to `Blank`
(`SettingsStore.cpp`), so those three places report it as `blank`, the same as
a never-written chip. Only the startup log line, `Settings load=read-failed
stored=blank`, tells the two apart, and it is emitted before USB has
enumerated; see [Startup](#startup).

A failure is never fatal: the firmware boots on defaults, and the next save
overwrites the bad image.

## Defaults

Defaults live in `Settings::Values` and must match the behaviour of the owning
code when nothing is stored. If the two disagree, a blank chip behaves
differently from a chip holding the default value, which is a difficult class of
bug to spot.

| Field | Default | Must match |
| --- | --- | --- |
| `adcLogEnabled` | `false` | `CurrentSenseTask::loggingEnabled_` |
| `adcDisplayEnabled` | `true` | `CurrentSenseTask::displayEnabled_` |
| `clockDisplayEnabled` | `true` | `ClockTask::displayEnabled_` |
| `clockTrimPpm` | `0` | `ClockTask::trimPpm_` |
| `hsiTrim` | `64` | The chip's reset `HSITRIM` (`HsiTrim::kDefault`); `AstroWeather_Init()` applies any other value |
| `lowBrightness` | `false` | `LowBrightness`'s `enabled`, and the reset level of `PB8` |
| `wifiSsid` | empty | — |
| `wifiPassword` | empty | — |
| `apiHost`, `apiPath` | empty | the built-in `APP_ST67_HTTP_HOST` / `APP_ST67_HTTP_PATH`, via `HostController::resolveApiTarget()` |

## Space budget

Within the 256-byte image, available payload is `256 - 6 = 250` bytes. Each record costs its value length
plus two bytes of framing.

| Content | Payload cost |
| --- | --- |
| `AdcFlags` | 3 |
| `ClockTrim`, only when an RTC or HSI trim is set | 6, or 7 with the HSI trim |
| `ClockFlags`, only when the clock display is off | 3 |
| `DisplayFlags`, only when low brightness is on | 3 |
| WiFi, typical (15-char SSID, 20-char password) | 39 |
| WiFi, worst case (32 + 63) | 99 |
| API host, only when saved (up to 64) | up to 66 |
| API path, only when saved (up to 32) | up to 34 |
| API key, only when saved (up to 32) | up to 34 |
| **Worst case total** | **249 of 250** |

A measured image on hardware with SSID `AstroNet` and a 13-character password
occupied 34 bytes, when the image was 128 bytes. With no WiFi configured the image is
9 bytes.

This is why the payload is TLV and not a packed struct. A struct would have to
reserve the worst case for credentials whether or not any were set, permanently
consuming 99 bytes, and the API target another 130.

When adding a setting, check the worst case still fits, and prefer omitting a
record over writing a default value.

The path is limited to 32 characters so that the API key fits beside it; with
a 64-character path the worst case would be 280. The real path,
`/device/astro/wroclaw`, has 21. When the next setting does not fit, the way
out is the upper 256 bytes of the 512-byte
part, which the image leaves unused (see [Storage Medium](#storage-medium)):
a payload over 255 bytes needs a wider `payloadLen`, which is a container
change with a version bump and a decoder that still reads version 1 (see
[When the version must change](#when-the-version-must-change)).

## Write Behaviour

`Settings::Store::save()` encodes the full 256-byte image, reads the current
contents, and writes only the 16-byte pages that differ. Toggling a single flag
therefore costs one page and one write cycle, roughly 5 ms, rather than all
16 pages of the image. The first save after the move from 128 bytes also
writes the upper pages, filling them with `0xFF` padding. The two working
images live in the `Store` object, not on the calling task's stack, since
`save()` runs on `MainLoopTask` (switch 2) as well as the console task.
If the read fails, every page is written rather than skipping the save.

The encoder always produces a full-length image with `0xFF` padding, so the
result is deterministic and no stale bytes are left behind a shortened payload.

Saves happen synchronously whenever a setting changes: from the console task, and for low brightness also from `MainLoopTask` when switch 2 is pressed. `save()` holds the store's lock across the read-compare-write, so two saves cannot interleave their pages.
The 24AA04H is rated for more than 1 million erase/write cycles, so per-change saves are not a
wear concern at console-command rates.

## Console Interface

The exact replies are in [Console.md](Console.md).

| Command | Effect |
| --- | --- |
| `settings show` | Print current values and the startup load result. The password is reported only as `<set>` or `<unset>`. |
| `settings save` | Force a write. |
| `settings defaults` | Reset all values to defaults and save. |
| `wifi set <ssid> [password]` | Store credentials, save, and test the connection. |
| `wifi test` | Connect with the stored credentials and report the result. |
| `wifi clear` | Drop stored credentials and save. |
| `adc log on\|off` | Toggle and save. |
| `adc display on\|off` | Toggle and save. |
| `time display on\|off` | Toggle and save. HostController only. |
| `time trim <ppm>` | Apply and save. HostController only. |
| `time hsi <0-127>` | Apply and save. HostController only. |
| `display low on\|off` | Apply and save. HostController only. |
| Switch 2 | Toggle low brightness and save. HostController only. |
| `api host <host>`, `api path <path>`, `api key <key>` | Check and save; used from the next fetch. HostController only. |
| `api default` | Drop the saved host, path and key and save. HostController only. |

The raw image can be inspected with `eeprom dump` and `eeprom read`, which is
the quickest way to confirm a new record encodes as intended. See
[Console.md](Console.md#eeprom).

## Code Layout

| File | Responsibility |
| --- | --- |
| `User/Inc/Settings/SettingsCodec.hpp` | Layout constants, `Tag`, `Values`, `DecodeResult` |
| `User/Src/Settings/SettingsCodec.cpp` | `encode()`, `decode()`, `crc16()`. Pure, no HAL |
| `User/Inc/Settings/SettingsStore.hpp` | `Store`, `LoadResult` |
| `User/Src/Settings/SettingsStore.cpp` | EEPROM read/write, page diffing |
| `User/Src/Console/SettingsCommand.cpp` | `settings` and `wifi` commands |
| `User/Src/Console/ApiCommand.cpp`, `LowBrightnessCommand.cpp` | `api` and `display low` commands, which also save |
| `User/Src/Astro/ApiTarget.cpp` | `resolveApiTarget()`: saved API host and path, or the built-in ones |
| `tests/SettingsCodecTests.cpp` | Native tests |

The codec is deliberately free of HAL dependencies so it builds and runs on the
host. Keep it that way: all EEPROM access belongs in `SettingsStore`.

### Tests

`tests/SettingsCodecTests.cpp` runs under the `NativeTests` preset alongside the
other native suites. It currently covers round trip, blank chip, a corrupted
byte, an unknown tag between known ones, an absent record, a record running past
the payload, an unrecognised container version, worst-case field lengths with
every optional record present, the empty-WiFi case, images written without the
clock or display records, an image written when the region was 128 bytes, the
API target costing nothing until set, and the one-record cost of clock trim,
clock display off and low brightness, the key's one-record cost and its
absence in an older image, a 40-byte path from the 64-character era being
dropped rather than truncated, and the HSI trim as the clock trim record's
fifth byte: one byte's cost, absent at its default, and ignored above 127.

The unknown-tag and absent-record cases are what pin down the compatibility
rules. Do not delete them.

`SettingsStore` is not tested: the page diff in `save()`, its write-everything
fallback when the read fails, and the read-failure path of `load()` have been
checked on hardware only.

## Startup

`Settings::Store::load()` is called from `AstroWeather_Init()`, which runs before
`osKernelStart()`. This is safe because EEPROM reads take no `osDelay` and the
I2C bus mutex is uncontended at that point, so acquiring it takes the
non-blocking path.

A saved HSI trim is applied right after the load, before the display refresh
starts; it has no effect, since the host runs from its crystal.

The outcome is logged, but not the values, since they include credentials. Note
that this log line is emitted before USB CDC has enumerated, so it is only
visible to a debugger attached over SWD. Use `settings show` to inspect the
loaded state from the console.

## Limitations

- **A torn write is detected but not recoverable.** Losing power during a save
  leaves a CRC mismatch, and the firmware falls back to defaults. The 512-byte
  part now has room to fix this, for example one image per 256-byte block with
  a sequence number, loading the newest valid copy and saving over the older.
  That is not implemented: it changes the container, so it would be container
  version 2.
- **Credentials are stored and transported in the clear.** The password
  crosses the USB console as typed, and `eeprom dump` and `eeprom read` print
  it from the chip. The firmware does not echo or log command lines: the
  `wifi set` reply repeats the SSID but gives the password only as
  `password=<set>`, and `settings show`, `status` and the startup log never
  print it. One exception: an unrecognised `settings` or `wifi` command is
  answered with `ERR unknown command '<first 40 characters>'`, so a mistyped
  `wifi set` can echo part of a password.
- **Unknown tags are not preserved across a save.** The image is re-encoded from
  the in-RAM `Values`, so any record this firmware does not recognise is
  dropped. Flashing an older build, saving, then flashing a newer one loses the
  newer settings.

## Worked Example

An image holding logging enabled, display disabled, SSID `AstroNet` and password
`hunter2secret`, read back with `eeprom read 000 30`:

```text
000: 41 57 3F 90 01 1C 01 01 01 10 08 41 73 74 72 6F
010: 4E 65 74 11 0D 68 75 6E 74 65 72 32 73 65 63 72
020: 65 74 FF FF FF FF FF FF FF FF FF FF FF FF FF FF
```

| Bytes | Meaning |
| --- | --- |
| `41 57` | Magic `AW` |
| `3F 90` | CRC-16 over the following 30 bytes |
| `01` | Container version 1 |
| `1C` | 28 payload bytes |
| `01 01 01` | `AdcFlags`, 1 byte, bit 0 set: logging on, display off |
| `10 08 41 73 74 72 6F 4E 65 74` | `WifiSsid`, 8 bytes, `AstroNet` |
| `11 0D 68 ... 74` | `WifiPassword`, 13 bytes |
| `FF ...` | Padding |

After `settings defaults`, the same array reads:

```text
000: 41 57 04 C2 01 03 01 01 02 FF FF FF FF FF FF FF
```

The WiFi records are gone entirely rather than being present and empty, leaving
a 3-byte payload.
