jakubprzybytek/AstroWeather/firmware/HostControllerA/docs/CubeMXCompliance.md

# CubeMX Compliance Migration Plan

## Goal

Restore the customized HostController behavior after fresh STM32CubeMX generation while respecting CubeMX ownership rules.

The governing rule is:

- Application code belongs in `User/Inc` and `User/Src`.
- Generated files may contain custom code only inside existing `USER CODE BEGIN` / `USER CODE END` regions.
- Generated and vendor files must not be modified elsewhere.
- The migration compared the tree against two local snapshots, `External/Clean` (freshly generated) and `External/Customized` (the previous customized tree). They were never committed and are not in the repository.

The current ST67 Wi-Fi design that resulted from this migration is described in [WiFi.md](WiFi.md).

The first milestone is a compiling, operational baseline. Memory-leak investigation and cold-restart optimization are intentionally deferred.

## ST Documentation Basis

This plan is consistent with the following ST documentation:

- [X-CUBE-ST67W61 Architecture](https://wiki.st.com/stm32mcu/wiki/Connectivity:X-CUBE-ST67W61_Architecture)
- [How to use X-CUBE-ST67W61 STM32CubeMX pack](https://wiki.st.com/stm32mcu/wiki/Connectivity:Wi-Fi_How_to_use_X_CUBE_ST67W61_STM32CubeMx_pack)
- [ST67W6X Echo Application](https://wiki.st.com/stm32mcu/wiki/Connectivity:Wi-Fi_ST67W6X_Echo_Application)

**2026-10-03:** the project now selects ST67 architecture **T01** without lwIP (`ST67_ARCH=W6X_ARCH_T01`); TCP/IP, DNS and TLS run in the module and the host uses the driver's `W6X_Net_*` sockets. The lwIP statements below record the T02 period (2026-08 to 2026-10) and the migration work done then; the rules about generated code are unchanged. See [ST67_HTTPS_Implementation_Plan.md](ST67_HTTPS_Implementation_Plan.md) for the switch.

Until 2026-10-03 the project selected ST67 architecture T02 with lwIP 2.2.1 on the STM32 host. ST documents that, for T02:

- lwIP owns TCP/IP and BSD sockets on the host;
- the ST Net and HTTP services are disabled;
- HTTP must be implemented on top of lwIP;
- the netif layer carries lwIP station and soft-AP traffic through `spi_iface`;
- `W61_MAX_SPI_XFER` must be 1520 bytes to avoid wasting dynamic memory.

This directly supports placing the application HTTP implementation under `User` rather than customizing the generated HTTP client. The project already configures `W61_MAX_SPI_XFER=1520U`.

ST also states that X-CUBE-ST67W61 USER CODE section coverage is intentionally limited and may not cover every customization. This reinforces the project rule that substantial application behavior belongs under `User/Inc` and `User/Src`.

## Current State

The migration started from a freshly generated tree, compared against a snapshot of the previous customized tree; neither snapshot is in the repository.

The regeneration removed custom lifecycle and HTTP changes. The User code has since been migrated away from the removed HTTP and network lifecycle APIs. HTTP now uses a User-owned synchronous GET implementation; runtime behavior and the complete cancellation contract remain to be validated.

SPI1 RX/TX DMA configuration was removed by the earlier regeneration and has now been restored through CubeMX. The regenerated configuration uses DMA1 Channel 1 for SPI1 RX and DMA1 Channel 2 for SPI1 TX. Both channels use high-priority, byte-aligned, normal-mode transfers with peripheral increment disabled and memory increment enabled. DMA initialization runs before SPI1 initialization, and both IRQ handlers dispatch to the correct HAL DMA handles at interrupt priority 3.

This matches ST's documented requirement for full-duplex master SPI with high-priority TX and RX DMA, memory increment enabled, and peripheral increment disabled. `ST67_RDY` is configured for rising and falling edge interrupts as documented. The SPI kernel clock is 16 MHz (HSI). The migration used a prescaler of 16 (1 MHz); since 2026-08-30 it is 8, producing a 2 MHz SPI clock, safely below ST's 40 MHz maximum.

The FreeRTOS heap is configured to 40,000 bytes, matching ST's minimum recommendation for a project generated from scratch.

The top-level `CMakeLists.txt` discovers the sources under `User/Src` and the shared `../Common/Src`, and includes `User/Inc` and `../Common/Inc`. New User modules are therefore picked up without modifying generated CMake files.

## Migration Status (2026-08-26)

Completed and build-checked:

- SPI1 RX/TX DMA configuration, DMA IRQ priority, initialization order, and IRQ dispatch were already restored by CubeMX and remain unchanged.
- Added the Cortex-M0+ FreeRTOS 10.3.1 interrupt-context compatibility macro in the preserved USER include section of `Core/Inc/FreeRTOSConfig.h`.
- Added `SPI_THREAD_STACK_SIZE=1536U` to the top-level target compile definitions. *(Later found to have no effect; see [ST67 driver task settings](#st67-driver-task-settings).)*
- Added the missing empty `logshell_ctrl.h` compatibility header under `User/Inc`; the generated TLS source includes this header but no current root source uses its API.
- Replaced the removed private station-status and network-running checks with the User-owned `St67NetworkAdapter`, which uses public W6X and lwIP interfaces, and made the default lifecycle persistent.
- `Debug` and `Release` build successfully. `git diff --check` passes.
- Hardware smoke test passed: ST67 initialization, callback registration, Wi-Fi association, DHCP, SPI/RDY traffic, HTTP GET (`200`, 83 bytes), and response CRC validation all completed successfully.
- The HTTP fetch task no longer overflows its 2560-byte stack; the observed post-request watermark was 848 bytes. HTTP transport buffers are heap-owned and were released after the request, with the batch heap returning from 39080 bytes to 39080 bytes.
- Diagnosed and corrected repeated HTTP-request failures: single client-triggered requests now use one persistent lifecycle cycle and leave the supported ST67/lwIP infrastructure initialized. The station still disconnects after each request, but the unsupported full `W6X_DeInit()` path is no longer used between requests.
- Hardware stress test passed: 100 persistent ST67 connectivity cycles completed with `pass=100 fail=0`; every cycle associated, obtained DHCP configuration, and disconnected without a lifecycle failure.
- The 100-cycle run remained stable at `heap=24752`, with a low-water mark of `19080` bytes and `tasks=12` during cycles. The final report showed `heapFree=30744`, `heapMin=19080`, `busyDrop=0`, `dropped=0`, `rxOverflow=0`, and `rxTrunc=0`; observed stack margins remained healthy.
- HTTP persistent stress test passed: with `APP_ST67_LIFECYCLE_MODE=3`, all 100 HTTP lifecycle cycles completed with `pass=100 fail=0`. Per-cycle heap remained `24752` bytes, the cycle low-water mark was `18944` bytes, and the final report showed `heapFree=30744`, `heapMin=18944`, `tasks=8/10`, and `St67HttpFetch` with `840` bytes remaining.

Current build status:

- Both configured build presets pass. The User-owned HTTP implementation currently uses bounded synchronous GET requests with socket send/receive timeouts.

Still pending:

- Runtime HTTP cancellation, total-timeout, malformed-response, oversized-response, and unreachable-host validation.
- USB CDC asynchronous transmit-buffer ownership review remains pending. The HTTP stress run ended with `dropped=0`, `busyDrop=13`, `rxOverflow=0`, and `rxTrunc=0`; the `busyDrop` count is debug-log backpressure, not an HTTP-cycle failure.

## Migration Inventory

| Area | Required action | Safe destination |
| --- | --- | --- |
| Application bootstrap | Retain the `AstroWeather_Init()` integration | Existing USER blocks in `Core/Src/main.c`; implementations in `User` |
| USB console | Retain the CDC bridge to `ConsoleService_OnUsbRxData()` | Existing USER blocks in `USB_Device/App/usbd_cdc_if.c`; implementation in `User` |
| SPI DMA | Complete: RX/TX DMA, DMA IRQs, and priority 3 regenerated and compile-checked | CubeMX `.ioc` configuration followed by regeneration |
| SPI task stack | **Complete**: use the larger ST67 stack requirement | `USER CODE BEGIN EC` block of `ST67W6X_Network_Driver/Target/w61_driver_config.h` |
| CM0+ FreeRTOS compatibility | **Complete**: provide `xPortIsInsideInterrupt()` for FreeRTOS older than 10.6 | Existing USER configuration section in `Core/Inc/FreeRTOSConfig.h` |
| SPI completion and RDY handling | **Complete for compile-time migration**: User-owned RDY rising-edge bridge calls `spi_on_txn_data_ready()`; hardware handshake validation remains | `User/Src/WiFi/St67SpiReady.cpp` |
| Station status | **Complete for compile-time migration**: dedicated User-owned adapter uses public W6X/lwIP interfaces; hardware validation remains | `User/Inc/WiFi/St67NetworkAdapter.hpp`, `User/Src/WiFi/St67NetworkAdapter.cpp` |
| HTTP request ownership | **Runtime stress-tested**: User-owned bounded synchronous GET completed 100 persistent HTTP lifecycle cycles with `pass=100 fail=0`; heap returned to `30744` bytes after the run. Cancellation, total deadline, and error-path coverage remain pending | `User/Inc/WiFi/HttpClient.hpp`, `User/Src/WiFi/HttpClient.cpp` |
| Network lifecycle | **Runtime validated**: the supported persistent ST67/lwIP infrastructure and repeated HTTP lifecycle completed 100 cycles with no failures or progressive heap loss; station disconnect still occurs after each request | `User/Src/WiFi/St67NetworkSession.cpp`, `User/Src/WiFi/St67HttpFetchTask.cpp`, `Appli/App/app_config.h` |
| Cold restart | Defer until supported teardown is available | Revisit only after public APIs or a fully User-owned replacement are identified |

## Phase 1: Restore the Generated Hardware Baseline

1. Complete: update the CubeMX configuration to restore SPI1 RX and TX DMA.
2. Complete: restore DMA interrupt generation at priority 3.
3. Complete: regenerate the project.
4. Complete: verify the generated DMA mapping, HAL links, initialization order, and IRQ dispatch.
5. **Complete:** added the ST-documented `xPortIsInsideInterrupt()` compatibility definition for this Cortex-M0+ and FreeRTOS 10.3.1 configuration in the preserved USER include section of `Core/Inc/FreeRTOSConfig.h`.
6. **Complete:** `SPI_THREAD_STACK_SIZE=1536U`. First added as a compile definition in the top-level `CMakeLists.txt`, which never took effect; now set in the driver's configuration header. See [ST67 driver task settings](#st67-driver-task-settings).
7. **Complete:** `Debug` and `Release` build successfully.

Do not manually recreate DMA handles, MSP links, IRQ forwarding, or peripheral initialization in generated files.

The DMA-specific generated units compile successfully. The FreeRTOS compatibility and stack-size fixes are in place, the network-session code uses public lwIP APIs, and the HTTP fetcher uses the User-owned GET implementation. Both build presets pass. Runtime validation remains outstanding.

## Phase 2: Remove Compile-Time Dependencies on Generated Extensions

### Station status adapter

**Complete for compile-time migration:** `St67NetworkAdapter` combines the public `W6X_WiFi_Station_GetState()` API with `netif_get_interface(NETIF_STA)` and supported lwIP netif fields/accessors. ST documents both station-state polling and asynchronous connected, disconnected, and got-IP events.

`St67NetworkSession.cpp` now uses this adapter instead of:

- `lwip_get_station_status()`
- `lwip_netifs_are_removed()`
- `net_if_is_running()`
- `net_if_outstanding_pbufs()`
- `MX_LWIP_DeInit()`

The adapter does not reach into private generated state. Hardware validation completed 100 persistent connect/disconnect cycles with no failures.

### Persistent lifecycle policy

**Complete for compile-time migration:** the default application lifecycle is now persistent rather than `APP_ST67_LIFECYCLE_SINGLE_FULL_SHUTDOWN`. The intended behavior is:

1. connect or wait for DHCP,
2. fetch data,
3. disconnect or release the session without destroying the stack,
4. repeat the operation.

This is the smallest compliant path because the previous full teardown depended on private state in generated and vendor modules.

## Phase 3: Move HTTP Behavior Behind a User-Owned Boundary

Do not restore the customized implementation directly into `LWIP/App/http_client.c`. Most of that customization was outside CubeMX USER blocks and will be overwritten again.

Add a User-owned HTTP implementation with the minimum behavior needed by `St67HttpFetcher`:

- one active request at a time,
- request cancellation,
- bounded request and response buffers,
- connect and receive timeouts,
- response-header and status validation,
- safe `Content-Length` handling,
- protection against oversized or malformed responses,
- exactly-once completion/error notification,
- cleanup of task, socket, TLS state, and allocated buffers on every path.

**Progress:** the User-owned synchronous GET implementation is complete enough for all three firmware builds and has passed both a hardware smoke test and a 100-cycle persistent HTTP stress test. `St67HttpFetcher.cpp` no longer calls `HTTP_Client_Cancel()` or `HTTP_Client_IsIdle()`. The client owns the socket, bounded request/response buffers, response-size checks, Content-Length validation, callback completion, and socket cleanup. Client-triggered requests retain the supported persistent network/lwIP infrastructure between requests after repeated DHCP failures exposed the previous full-shutdown path. External cancellation, an explicit total deadline, and runtime error-path tests remain pending.

The initial implementation may support only the HTTP method and transport required by the application. HTTPS and less-used POST/PUT behavior should be added only when required by an actual caller.

## Phase 4: Restore Callback Bridges

Keep all substantive behavior in User-owned source files. Generated callbacks should only make minimal calls from existing USER blocks.

**Progress:** the User-owned `HAL_GPIO_EXTI_Rising_Callback()` bridge for `ST67_RDY_Pin` now calls the public `spi_on_txn_data_ready()` hook. All three build presets pass, and hardware smoke testing confirmed successful ST67 initialization, Wi-Fi/DHCP, and HTTP traffic without the former `sem_if_ready` timeout. A 100-cycle persistent connectivity stress test also passed; repeated HTTP transaction and error-path validation remain pending.

Expected bridges include:

- SPI transaction completion to the ST67 User-owned transport state.
- GPIO RDY rising edge to the User-owned ST67 notification path.
- Optional recoverable SPI error notification.

The generated `spi_port.c` already provides USER blocks around SPI completion and error callbacks. Do not add duplicate HAL callback definitions outside those hooks. The button-related falling-edge callback is owned by `../Common/Src/Utils/SwitchInput.cpp`; the ST67 rising-edge bridge is in `User/Src/WiFi/St67SpiReady.cpp`.

## Explicitly Deferred

The following customized behavior should not be migrated in the initial pass because it requires prohibited changes to generated or vendor internals:

- full `MX_LWIP_DeInit()` behavior,
- private netif and timer cleanup,
- W61 initialization failure cleanup inside vendor code,
- private SPI error-state propagation,
- customized HTTP internals inside the generated HTTP client.

ST does provide public `W6X_WiFi_DeInit()`, `W6X_Netif_DeInit()`, and `W6X_DeInit()` APIs. These should be used where appropriate, but they do not deinitialize the CubeMX-generated lwIP timers, threads, and netifs. Full cold-restart support can therefore be reconsidered only if the remaining lwIP teardown can be performed through supported public APIs or if that layer is replaced entirely by a maintained User-owned module. A wrapper is insufficient when the required state is `static` inside generated files.

## Instrumentation To Omit

Do not migrate memory-leak investigation code at this stage:

- heap, task, and pbuf checkpoint logging,
- lwIP netif/timer/AP-table allocation counters,
- Wi-Fi context and event allocation counters,
- modem semaphore and buffer counters,
- command-handler mutex counters,
- SPI queue/event allocation counters,
- allocation summaries added to deinitialization functions,
- repeated cold-restart stress instrumentation.

Retain only operational safeguards needed for correctness, especially buffer bounds, timeout handling, and deterministic cleanup.

## Validation Gates

After each CubeMX regeneration:

```text
git diff --check
git diff --stat
git diff --name-status
git diff -- HostControllerA.ioc Core cmake/stm32cubemx
```

Build gates:

1. `Debug`
2. `Release`
3. The `../DisplayController` project's `Debug`, whenever `../Common` changed

The configured build toolchain is GNU Arm Embedded with the Ninja generator. The STM32Cube bundle provides CMake, Ninja, and the compiler; the versioned directories differ between installations. For example:

- CMake: `C:\Users\<user>\AppData\Local\stm32cube\bundles\cmake\4.3.1+st.1\bin\cmake.exe`
- Ninja: `C:\Users\<user>\AppData\Local\stm32cube\bundles\ninja\1.13.2+st.1\bin\ninja.exe`
- GNU Arm: `C:\Users\<user>\AppData\Local\stm32cube\bundles\gnu-tools-for-stm32\14.3.1+st.2\bin\arm-none-eabi-gcc.exe`

See [Development.md](Development.md#prerequisites) for putting them on `PATH` or using the bundled Cube CMake.

Build a preset with:

```text
cmake --build --preset Debug
```

Runtime gates:

- SPI DMA transfers complete and their interrupts reach the driver.
- DHCP and station-status transitions are observed through public interfaces.
- Repeated persistent connect/fetch/disconnect cycles do not create tasks or sockets indefinitely.
- HTTP success, timeout, malformed header, oversized response, and unreachable-host cases complete exactly once.
- HTTP buffers and sockets are released on success, cancellation, timeout, and error.
- The legacy probe task (`St67ProbeTask`) never runs concurrently with the official driver. It is currently never started.

Do not make cold-restart heap stability a release gate until a compliant teardown implementation exists.

## Risks and Decisions

- The full-shutdown lifecycle, the default before the migration, is incompatible with the smallest safe migration path. Resolved: the default is now `APP_ST67_LIFECYCLE_HTTP_PERSISTENT_STRESS`, and client fetches always use the persistent lifecycle whatever the mode; see [WiFi.md](WiFi.md#lifecycle).
- The generated HTTP client does not provide the customized ownership and cancellation contract required by the current User code.
- The existing build artifacts may contain a stale compile database; a fresh CMake build is required for trustworthy diagnostics.
- The STM32Cube toolchain is now available on `PATH`; fresh builds should be used to replace stale build-artifact diagnostics.
- USB CDC logging currently reports substantial cumulative `USBD_BUSY` drops under the hardware run; this affects debug observability but did not prevent the HTTP smoke test from completing.

## ST67 driver task settings

The ST67 driver takes three settings from `#ifndef` defaults: `SPI_THREAD_STACK_SIZE` and `SPI_THREAD_PRIO` in `spi_iface.c`, and `W61_MDM_RX_TASK_PRIO` in `w61_at_common.h`. CubeMX does not expose them in the `.ioc`. They are overridden in the `USER CODE BEGIN EC` block of `ST67W6X_Network_Driver/Target/w61_driver_config.h`, which the driver includes ahead of those defaults and which survives regeneration.

Definitions on the top-level CMake target do **not** reach the driver: it is compiled in the generated `STM32_Drivers` object library, which receives only the CubeMX defines. The earlier `SPI_THREAD_STACK_SIZE=1536U` target definition was silently ignored for that reason, so the driver ran with its 768-byte default until the setting moved into the header.

| Setting | Default | Project value | Why |
| --- | --- | --- | --- |
| `SPI_THREAD_STACK_SIZE` | 768 | 1536 | Larger ST67 stack requirement, as above. |
| `SPI_THREAD_PRIO` | 53 | 46 | Below `DisplayRefresh`, then at 48. |
| `W61_MDM_RX_TASK_PRIO` | 54 | 47 | Below `DisplayRefresh`; kept one above the SPI engine as in the defaults. |

At their default priorities the two driver tasks pre-empted the display multiplexing task, holding a slot for up to 14 ms instead of 4 ms during WiFi activity, which was visible as the whole display flashing during a refresh. Measured by timing slot switches in the display task: the longest gap fell from 14 ms with four late switches to 8 ms with one per refresh, with WiFi fetches still succeeding. The remaining short stall happens during connect and was not traced.

That stall was LwIP's `netif` task, which the driver creates at `NETIF_TASK_PRIORITY` 50, above the display's 48. The value is a plain `#define` in the generated `LWIP/App/lwip_netif.h`, outside any USER CODE block and without an `#ifndef` guard, so it cannot be overridden in a way that survives regeneration. `DisplayRefresh` was raised to `osPriorityRealtime7` (55) instead, above every driver task. Measured with the display's gray-level test on 2026-09-26: the display task's longest wait during an astro refresh fell from 4.5-5.4 ms, every one caught with `netif` running, to under 1 ms. The refresh has since moved into the TIM2 interrupt altogether, so no task priority is involved any more; see [Display.md](Display.md#refresh-operation).

## Linker script: retained RAM

`STM32G0B1xx_FLASH.ld` has a user change: the `RAM` region is 139 KiB, and the
last 5 KiB are a `NOINIT` region holding the `.noinit` section, for the error
log that survives a reset ([Console.md](Console.md#error-log)). Both changes are
marked `USER`. CubeMX regenerates the linker script only when asked to; if it
ever does, re-apply them, or the log silently stops surviving resets (the
build still links, with `.noinit` placed in `RAM` and cleared at startup).

## Display refresh timer and DMA

Set in CubeMX on 2026-09-27 for the interrupt-driven refresh with brightness levels ([Display.md](Display.md#refresh-operation)):

| Setting | Host (`HostControllerA.ioc`) | DisplayController (`DisplayController.ioc`) |
| --- | --- | --- |
| Refresh timer | TIM2: prescaler 15 (1 MHz count), period 3999 (placeholder), preload off, update interrupt at priority 3 | TIM6: the same |
| Display SPI DMA | `SPI3_TX` on DMA1 channel 4, memory to peripheral, byte/byte, memory increment, normal mode, priority high; its interrupt (`DMA1_Ch4_7_DMA2_Ch1_5_DMAMUX1_OVR`) at priority 3 | `SPI1_TX` on DMA1 channel 1, the same settings and `DMA1_Channel1` interrupt |

The DMA interrupt must stay enabled: `HAL_SPI_Transmit_DMA()` finishes its state machine in the transfer-complete interrupt, and the next transfer is refused as busy without it. The timer's period is rewritten by the refresh interrupt every pass, so the CubeMX value only sets the first pass; the prescaler and the disabled preload are what matter.

Verify any change here with a preprocessor dump of a driver unit, for example `spi_iface.c` from `compile_commands.json` with `-E -dM`, since a misplaced override fails silently.
