jakubprzybytek/AstroWeather/firmware/DisplayController/User/Inc/DisplayController.hpp

/*
 * DisplayController.hpp
 *
 * Application entry point, called from main.c after osKernelInitialize() and
 * before osKernelStart().
 */

#ifndef INC_DISPLAYCONTROLLER_HPP_
#define INC_DISPLAYCONTROLLER_HPP_

#ifdef __cplusplus
extern "C" {
#endif

extern void DisplayController_Init(void);

#ifdef __cplusplus
}
#endif

#endif /* INC_DISPLAYCONTROLLER_HPP_ */
