jakubprzybytek/AstroWeather/firmware/HostControllerA/Appli/App/app_config.h

#ifndef APP_CONFIG_H
#define APP_CONFIG_H

#if defined(__has_include)
#if __has_include("app_credentials.h")
#include "app_credentials.h"
#endif
#endif

#define APP_ST67_STARTUP_DELAY_MS 4000U
#define APP_ST67_SCAN_TIMEOUT_MS 15000U
#define APP_ST67_SCAN_MAX_RESULTS 20U
#define APP_ST67_DHCP_TIMEOUT_MS 15000U
#define APP_ST67_DISCONNECT_TIMEOUT_MS 12000U
#define APP_ST67_SHUTDOWN_SETTLING_DELAY_MS 100U
#define APP_ST67_COLD_RESTART_DELAY_MS 1000U
#define APP_ST67_HTTP_PORT 80U
#define APP_ST67_HTTPS_PORT 443U
/* 1: HTTPS on APP_ST67_HTTPS_PORT with the module verifying the server against
   TrustedCa; 0: plain HTTP on APP_ST67_HTTP_PORT, for bench diagnostics only. */
#ifndef APP_ST67_HTTP_USE_TLS
#define APP_ST67_HTTP_USE_TLS 1
#endif
/* Bench only (cmake -DAPP_ST67_TLS_BENCH_ANCHOR_ISRG=ON): trust ISRG Root X1
   instead of Amazon Root CA 1, for the badssl.com certificate failure cases. */
#ifndef APP_ST67_TLS_BENCH_ANCHOR_ISRG
#define APP_ST67_TLS_BENCH_ANCHOR_ISRG 0
#endif
#define APP_ST67_DNS_TIMEOUT_MS 5000U
#define APP_ST67_HTTP_IO_TIMEOUT_MS 5000U
#define APP_ST67_HTTP_TOTAL_TIMEOUT_MS 15000U
#define APP_ST67_HTTP_MAX_HEADER_BYTES 2048U
#define APP_ST67_HTTP_MAX_RESPONSE_BYTES 4096U

#define APP_ST67_LIFECYCLE_SINGLE_FULL_SHUTDOWN 0U
#define APP_ST67_LIFECYCLE_PERSISTENT_STRESS    1U
#define APP_ST67_LIFECYCLE_COLD_RESTART_STRESS  2U
#define APP_ST67_LIFECYCLE_HTTP_PERSISTENT_STRESS 3U

#ifndef APP_ST67_LIFECYCLE_MODE
#define APP_ST67_LIFECYCLE_MODE APP_ST67_LIFECYCLE_HTTP_PERSISTENT_STRESS
#endif

#define APP_ST67_PERSISTENT_STRESS_CYCLES 100U
#define APP_ST67_COLD_RESTART_STRESS_CYCLES 20U
#define APP_ST67_HTTP_PERSISTENT_STRESS_CYCLES 100U
#define APP_ST67_INTER_CYCLE_DELAY_MS 1000U

#ifndef APP_ST67_WIFI_SSID
#define APP_ST67_WIFI_SSID ""
#endif

#ifndef APP_ST67_WIFI_PASSWORD
#define APP_ST67_WIFI_PASSWORD ""
#endif

#ifndef APP_ST67_HTTP_HOST
#define APP_ST67_HTTP_HOST ""
#endif

#ifndef APP_ST67_HTTP_PATH
#define APP_ST67_HTTP_PATH ""
#endif

/* The API's device key, sent as ?key=; empty sends none. */
#ifndef APP_ST67_HTTP_KEY
#define APP_ST67_HTTP_KEY ""
#endif

#ifndef APP_ST67_HTTP_EXPECTED_CONTENT_TYPE
#define APP_ST67_HTTP_EXPECTED_CONTENT_TYPE "text/plain; charset=utf-8"
#endif

#endif /* APP_CONFIG_H */
