jakubprzybytek/AstroWeather/firmware/HostControllerA/User/Inc/AstroWeather.hpp

/*
 * AstroWeather.hpp
 *
 *  Created on: 26 lip 2026
 *      Author: jakub
 */

#ifndef INC_ASTROWEATHER_HPP_
#define INC_ASTROWEATHER_HPP_

#ifdef __cplusplus
extern "C" {
#endif

extern void AstroWeather_Init();

#ifdef __cplusplus
}
#endif

#endif /* INC_ASTROWEATHER_HPP_ */
