jakubprzybytek/AstroWeather/firmware/HostControllerA/User/Inc/Astro/AstroDataRefreshTask.hpp

#pragma once

#include <Astro/AstroData.hpp>
#include <Astro/AstroProgressBar.hpp>
#include <Astro/RefreshSchedule.hpp>
#include <WiFi/St67FetchTypes.hpp>
#include <Utils/Task.hpp>

#include "app_config.h"

#include <cstdint>

namespace Display {
class Display;
}

namespace HostController {

enum class RefreshTrigger : uint8_t
{
    Switch1,
    Console,
    Scheduled,
    WifiTest,  // 'wifi set' / 'wifi test': a refresh used to exercise the credentials
    Test,      // 'astro test': one fetch of the server's demo forecast, kTestPath
};

// The server's demo forecast: every display variant, with the real time.
constexpr const char* kTestPath = "/device/astro/test";

enum class RefreshRequestResult : uint8_t
{
    Accepted,
    Busy,
    Unavailable,
};

// How the most recent refresh ended, for status reporting. The log's
// "AstroDataRefresh complete" line is printed whatever the outcome, so it is not
// evidence of success on its own.
enum class RefreshOutcome : uint8_t
{
    Never,           // no refresh has run since boot
    Ok,              // fetched, verified, parsed and published
    FetchFailed,     // ST67/network/HTTP failure; see fetchStatus and httpStatus
    IntegrityFailed, // payload CRC did not match
    ParseFailed,
    PublishFailed,
};

struct RefreshSummary
{
    RefreshOutcome outcome = RefreshOutcome::Never;
    RefreshTrigger trigger = RefreshTrigger::Scheduled;
    St67FetchStatus fetchStatus = St67FetchStatus::Success;
    uint16_t httpStatus = 0U;
    uint32_t finishedTick = 0U;  // osKernelGetTickCount() when it finished
    bool running = false;
    // From the last response that parsed, which a later failure leaves alone.
    bool fetchTimesKnown = false;
    AstroFetchTime lastWeatherFetch{};
    std::array<AstroFetchTime, kAuroraFeedCount> lastAuroraFetch{};
};

// Where the scheduled refresh stands, for status reporting.
struct ScheduleSummary
{
    bool timeSet = false;         // false: the next slot is not known yet
    uint32_t nextSlot = 0U;       // seconds since 2000, local
    bool hasSuccess = false;
    uint32_t lastSuccess = 0U;    // seconds since 2000, local
    uint32_t failures = 0U;       // consecutive, since the last success
    uint32_t retryInMs = 0U;      // with failures: until the next attempt
    bool waitingForNextSlot = false;  // failed for want of WiFi credentials
    uint32_t intervalMinutes = 360U;  // 60 on a storm night
};

// 3.75 KB: the parsed forecast (~700 B), the clock sync and their formatted log
// lines all sit on this stack. 2 KB overflowed once the sync was added.
class AstroDataRefreshTask : public Task<3840>
{
public:
    static AstroDataRefreshTask& instance();

    void init(Display::Display* display);
    RefreshRequestResult requestRefresh(RefreshTrigger trigger);
    // Safe to call from any task.
    RefreshSummary lastRefresh() const;
    ScheduleSummary schedule() const;

protected:
    void run() override;

private:
    AstroDataRefreshTask();

    void executeRefresh(RefreshTrigger trigger);
    bool fetchPayload();
    bool publishDisplay(const AstroData& data);

    // Scheduled refresh; see RefreshSchedule. Checked each time run() wakes,
    // at least every kScheduleCheckMs.
    static RefreshSchedule::Clock readClock();
    void checkSchedule();
    void recordScheduleOutcome(RefreshOutcome outcome, St67FetchStatus fetchStatus);

    // Progress bar on the local board's bottom matrix row. Drawn from this task
    // only, while it waits for the WiFi task, so the WiFi task never touches the
    // display. The patterns and timing are AstroProgressBar's.
    static void onFetchProgress(FetchStage stage, void* context);
    void showProgressRow(const AstroProgressBar::Row& row);
    void startIndicator(AstroProgressBar::Indicator::Kind kind, uint8_t failedSegment);
    void clearIndicator();

    static constexpr uint32_t kFlagRun = 1U << 0;
    static constexpr uint32_t kScheduleCheckMs = 60000U;

    Display::Display* display_ = nullptr;
    uint8_t responseBuffer_[APP_ST67_HTTP_MAX_RESPONSE_BYTES]{};
    St67FetchRequest request_{};
    RefreshTrigger trigger_ = RefreshTrigger::Scheduled;
    volatile bool active_ = false;
    RefreshSummary last_{};
    // Written by this task only; read by others through schedule().
    RefreshSchedule::Scheduler scheduler_{};
    AstroProgressBar::Indicator indicator_{};
    // What showProgressRow() last drew, or none: before the first draw, and
    // after a publish drew the aurora row over it.
    static constexpr AstroProgressBar::Row kNoRowShown{0xFFFFFFFFU, 0xFFFFFFFFU};
    AstroProgressBar::Row shownRow_ = kNoRowShown;
    uint8_t loggedStage_ = 0xFFU;
};

const char* refreshTriggerName(RefreshTrigger trigger);
const char* refreshOutcomeName(RefreshOutcome outcome);
const char* fetchStatusName(St67FetchStatus status);

} // namespace HostController
