jakubprzybytek/AstroWeather/firmware/DisplayController/User/Inc/DisplayApp.hpp

#pragma once

#include <Display/DisplayBoard.hpp>
#include <FrameAssembler.hpp>
#include <I2cTarget.hpp>
#include <NoDataTimer.hpp>
#include <TimelineFollower.hpp>
#include <Utils/Task.hpp>

#include <cstdint>

// Decides what the board shows: the boot screens, the host's data with its
// blink and level attributes, "no data" before the first frame and after the
// data goes stale, and the switch-driven test screens. Owns no hardware; the
// refresh itself runs from PcbDisplayBoard's timer interrupt.
// 2048 B: show() -> submit() -> encodePasses() needs about 1 KB with the context
// switch frame (measured with -fstack-usage); 1024 overflowed on the first show().
class DisplayApp : public Task<2048> {
public:
    static constexpr uint32_t kFlagFrame = 1U << 0;
    static constexpr uint32_t kFlagSwitch1 = 1U << 1;
    static constexpr uint32_t kFlagSwitch2 = 1U << 2;
    static constexpr uint32_t kFlagSync = 1U << 3;

    // Longer than the host's 6-hour refresh interval: the host sends nothing
    // between refreshes, so a shorter timeout would show "no data" most of
    // the day. The host re-sends nothing older (Display::kContentLifetimeMs).
    static constexpr uint32_t kNoDataTimeoutMs = Display::kContentLifetimeMs;

    DisplayApp(Display::DisplayBoard& board, I2cTarget& link, TimelineFollower& timeline);

protected:
    void run() override;

private:
    enum class Screen : uint8_t { Data, AllSegments, Identify, Address };

    static constexpr uint32_t kAddressScreenMs = 3000U;
    static constexpr uint32_t kTestScreenMs = 60000U;
    static constexpr uint32_t kPollMs = 1000U;

    bool receiveFrames(uint32_t now);
    void setScreen(Screen screen, uint32_t now);
    bool screenTimedOut(uint32_t now) const;
    void show();
    void publishRefreshStats();

    Display::DisplayBoard& board_;
    I2cTarget& link_;
    TimelineFollower& timeline_;
    DisplayController::NoDataTimer noData_{kNoDataTimeoutMs};
    DisplayController::FrameAssembler frames_;
    Screen screen_ = Screen::Data;
    uint32_t screenSince_ = 0U;
};
