jakubprzybytek/AstroWeather/firmware/Common/Src/Device/SCT2xxx.cpp

#include <Device/SCT2xxx.hpp>

SCT2xxx::SCT2xxx(SPI_HandleTypeDef* spi,
                 GPIO_TypeDef* enablePort,
                 uint16_t enablePin,
                 GPIO_TypeDef* latchPort,
                 uint16_t latchPin)
    : spi_(spi),
      enablePort_(enablePort),
      enablePin_(enablePin),
      latchPort_(latchPort),
      latchPin_(latchPin) {}

HAL_StatusTypeDef SCT2xxx::shift(const uint8_t* data, uint16_t size)
{
    return HAL_SPI_Transmit(spi_, const_cast<uint8_t*>(data), size, HAL_MAX_DELAY);
}

HAL_StatusTypeDef SCT2xxx::shiftDma(const uint8_t* data, uint16_t size)
{
    return HAL_SPI_Transmit_DMA(spi_, const_cast<uint8_t*>(data), size);
}

bool SCT2xxx::busy() const
{
    return HAL_SPI_GetState(spi_) != HAL_SPI_STATE_READY;
}

void SCT2xxx::latch()
{
    HAL_GPIO_WritePin(latchPort_, latchPin_, GPIO_PIN_SET);
    HAL_GPIO_WritePin(latchPort_, latchPin_, GPIO_PIN_RESET);
}

HAL_StatusTypeDef SCT2xxx::send(const uint8_t* data, uint16_t size)
{
    const HAL_StatusTypeDef status = shift(data, size);
    if (status != HAL_OK) {
        return status;
    }
    latch();
    return HAL_OK;
}

HAL_StatusTypeDef SCT2xxx::send(uint8_t value)
{
    return send(&value, 1U);
}

void SCT2xxx::enable()
{
    HAL_GPIO_WritePin(enablePort_, enablePin_, GPIO_PIN_RESET);
}

void SCT2xxx::disable()
{
    HAL_GPIO_WritePin(enablePort_, enablePin_, GPIO_PIN_SET);
}
