jakubprzybytek/AstroWeather/firmware/HostControllerA/User/Inc/WiFi/St67ProbeTask.hpp

#ifndef INC_HOSTCONTROLLER_ST67PROBETASK_HPP_
#define INC_HOSTCONTROLLER_ST67PROBETASK_HPP_

namespace HostController {

void StartSt67ProbeTask();
void TriggerSt67Probe();
void TriggerSt67CwlapProbe();

}  // namespace HostController

#endif /* INC_HOSTCONTROLLER_ST67PROBETASK_HPP_ */
