jakubprzybytek/AstroWeather/firmware/Bypass/User/Inc/st67_mode.h

#ifndef ST67_MODE_H
#define ST67_MODE_H

#include <stdint.h>

typedef enum {
  ST67_MODE_MANUFACTURE = 0u,
  ST67_MODE_BOOTLOADER = 1u
} St67Mode;

#define ST67_DEFAULT_MODE_MANUFACTURE 0u
#define ST67_DEFAULT_MODE_BOOTLOADER  1u

#ifndef ST67_DEFAULT_MODE
#define ST67_DEFAULT_MODE ST67_DEFAULT_MODE_MANUFACTURE
#endif

#if (ST67_DEFAULT_MODE != ST67_DEFAULT_MODE_MANUFACTURE) && \
  (ST67_DEFAULT_MODE != ST67_DEFAULT_MODE_BOOTLOADER)
#error "ST67_DEFAULT_MODE must be MANUFACTURE (0) or BOOTLOADER (1)."
#endif

void ST67_EnterMode(St67Mode mode);

#endif /* ST67_MODE_H */
