jakubprzybytek/AstroWeather/firmware/Bypass/User/Inc/bridge.h

#ifndef BRIDGE_H
#define BRIDGE_H

#include <stdbool.h>
#include <stdint.h>

void Bridge_Init(void);
void Bridge_Process(void);
void Bridge_OnUsbRx(const uint8_t *data, uint32_t length);
void Bridge_OnUsbTxComplete(void);
void Bridge_OnHostConnectionChanged(bool dtr_asserted);
void Bridge_SetTxLed(bool on);
void Bridge_SetRxLed(bool on);

#endif /* BRIDGE_H */
